anatoliegolovco/s4/reference/schematics/sintez2-keyboard.jpg

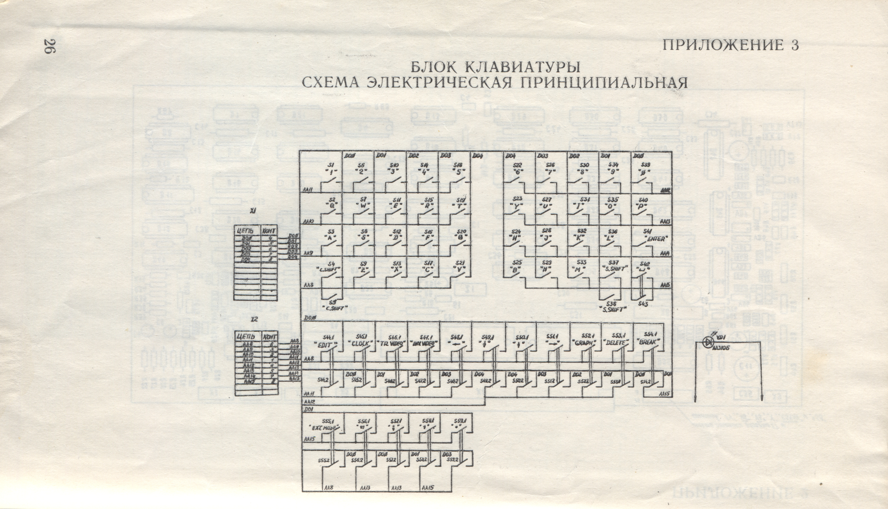
reference/schematics/sintez2-keyboard.jpg
