anatoliegolovco/s4/docs/ledger/architecture/README.md

# Topic: architecture

- **Created:** 2026-06-13
- **Status:** active

## Scope

Hardware/behavioral architecture decisions for the recreation and its model:
memory, DRAM timing, video arbitration, clock domains, and faithful-vs-improved
build targets.

## Questions

| Question file | Title | Status | Opened | Resolved |
| --- | --- | --- | --- | --- |
| [`dram-faithful-vs-improved.md`](./dram-faithful-vs-improved.md) | Faithful К565РУ5 timing vs modern SRAM in hardware? | open | 2026-06-13 | — |
| [`bank-switching-ram-size.md`](./bank-switching-ram-size.md) | How much RAM / what bank-switching scheme? | open | 2026-06-13 | — |
| [`schematic-bom-wiring-extraction.md`](./schematic-bom-wiring-extraction.md) | Mainboard BOM and wiring from the schematic | open | 2026-06-13 | — |
