anatoliegolovco/s4/docs/ledger/tooling/README.md

# Topic: tooling

- **Created:** 2026-06-13
- **Status:** active

## Scope

The tool stack and the zero-click control plane: KiCad, SimulIDE, ngspice, the
KiCad↔SimulIDE bridge, and how the LLM automates them through text.

## Questions

| Question file | Title | Status | Opened | Resolved |
| --- | --- | --- | --- | --- |
| [`schematic-automation-strategy.md`](./schematic-automation-strategy.md) | How does the LLM automate KiCad schematics in 2026? | resolved | 2026-06-13 | 2026-06-13 |
| [`cpu-soft-core-choice.md`](./cpu-soft-core-choice.md) | TV80 or A-Z80 for the simulation core? | open | 2026-06-13 | — |
