anatoliegolovco/s4/reference/board/sintez2-element-placement.jpg

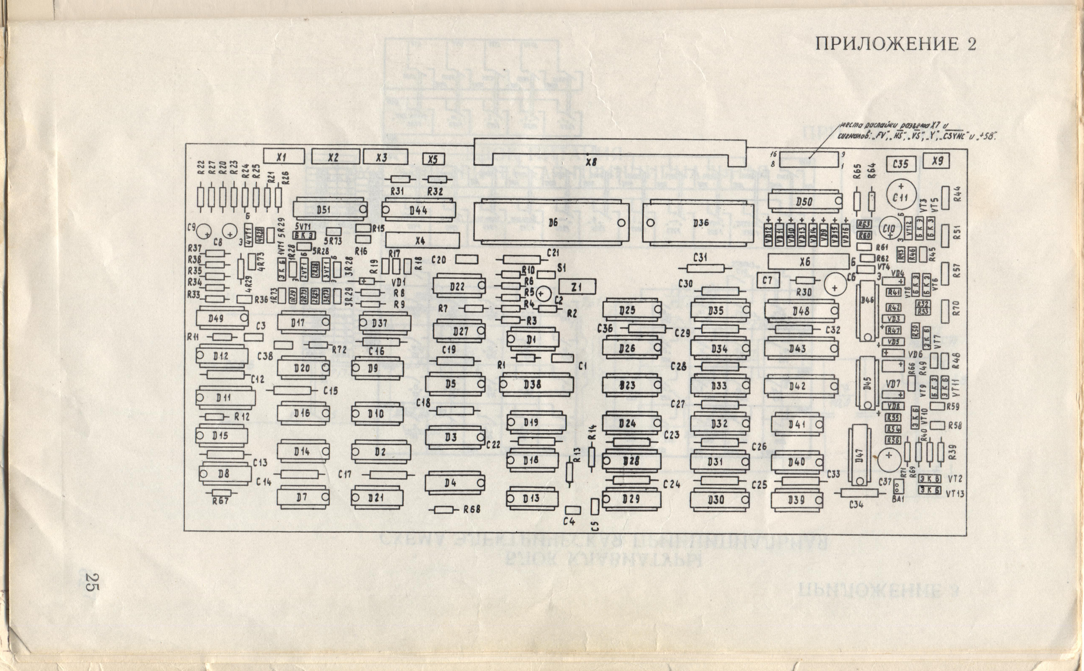
reference/board/sintez2-element-placement.jpg
