anatoliegolovco/s4/reference/photos/betadisk-original.png

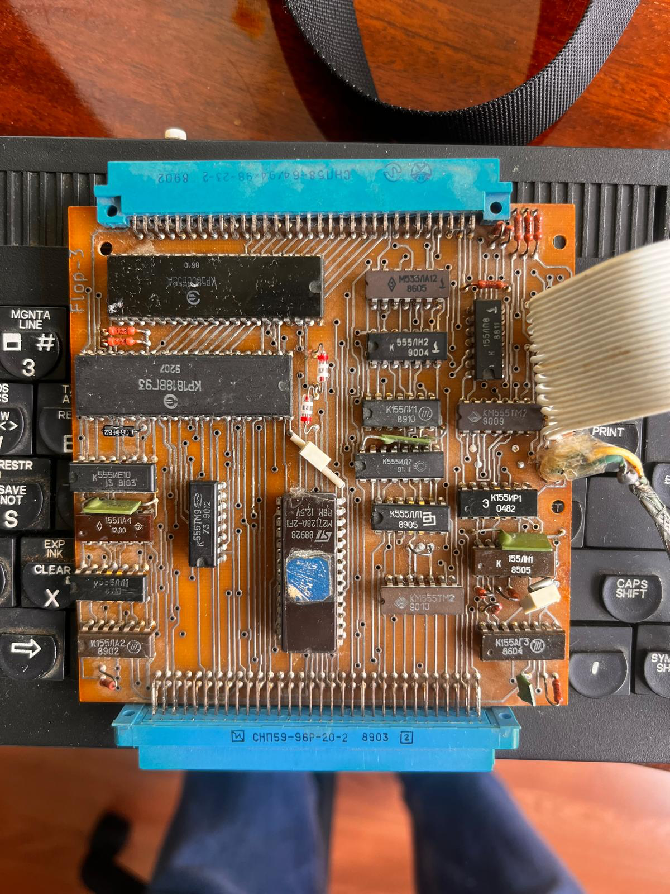
reference/photos/betadisk-original.png
