anatoliegolovco/s4/reference/photos/sintez2-board-habr.jpg

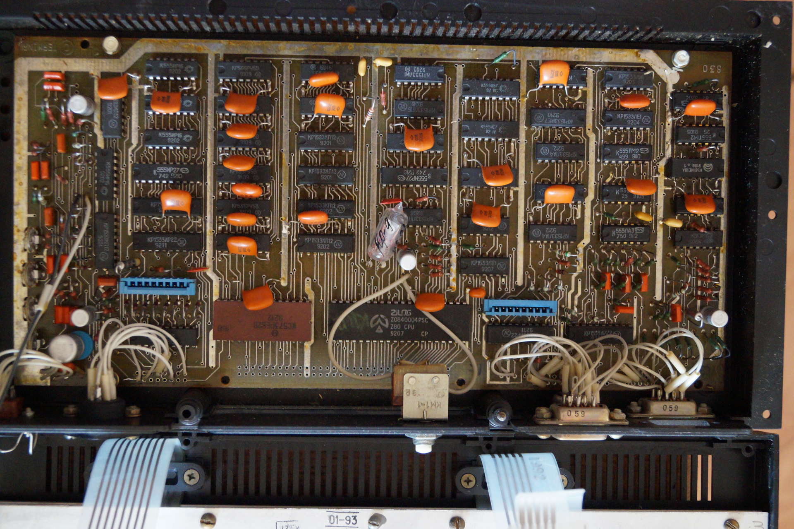
reference/photos/sintez2-board-habr.jpg
