anatoliegolovco/s4/reference/photos/sintez2-board-priborazbor.jpg

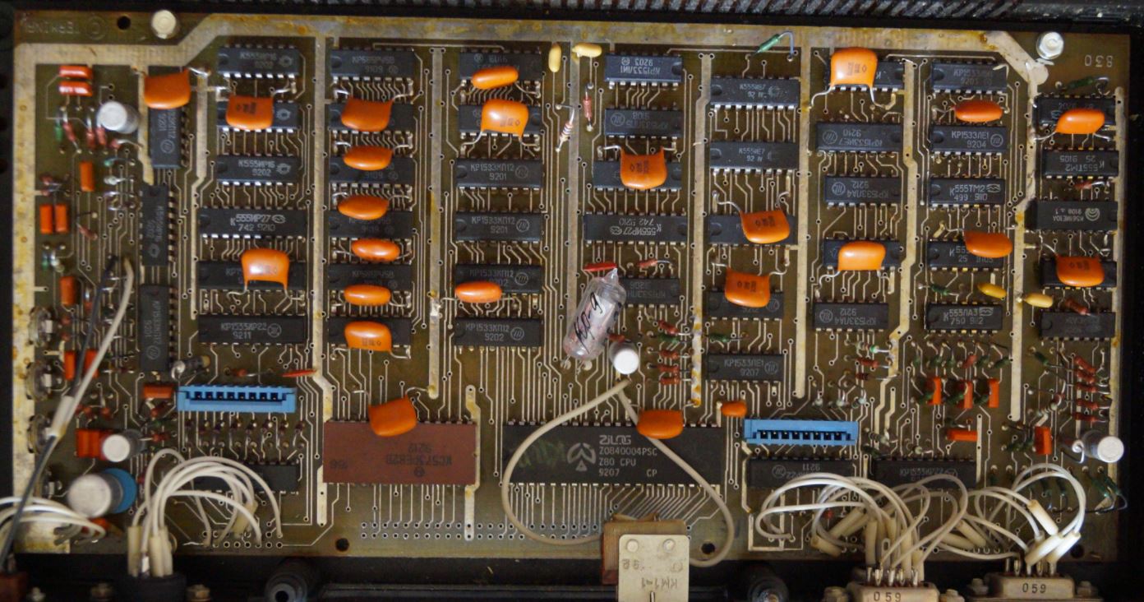
reference/photos/sintez2-board-priborazbor.jpg
