anatoliegolovco/s4/reference/photos/sintez2-rear-panel.jpg

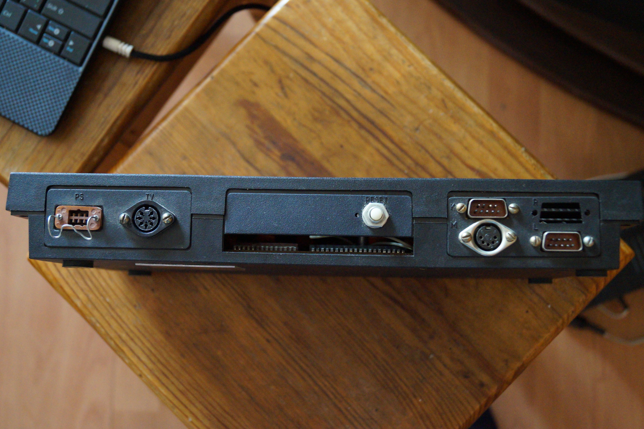
reference/photos/sintez2-rear-panel.jpg
