anatoliegolovco/s4/reference/photos/sintez128.jpg

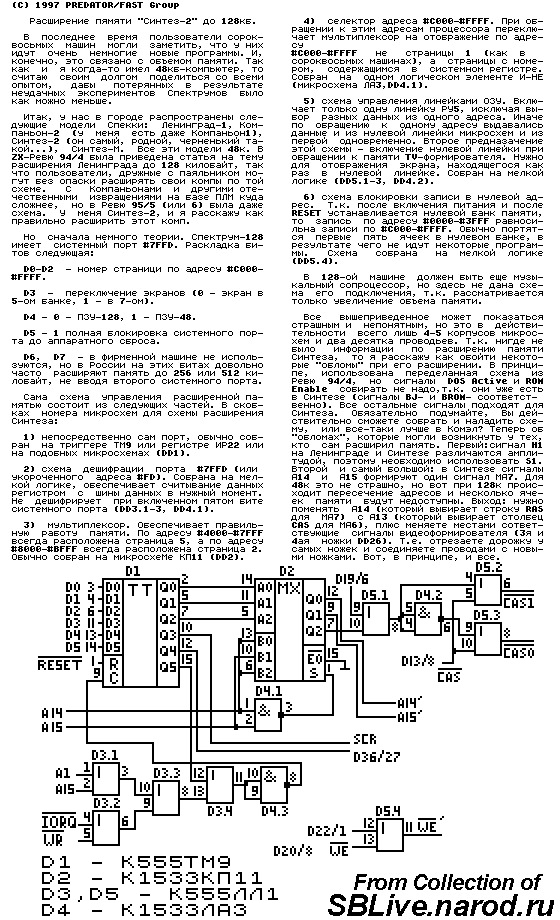
reference/photos/sintez128.jpg
