anatoliegolovco/s4/reference/pinouts/video-pinout.png

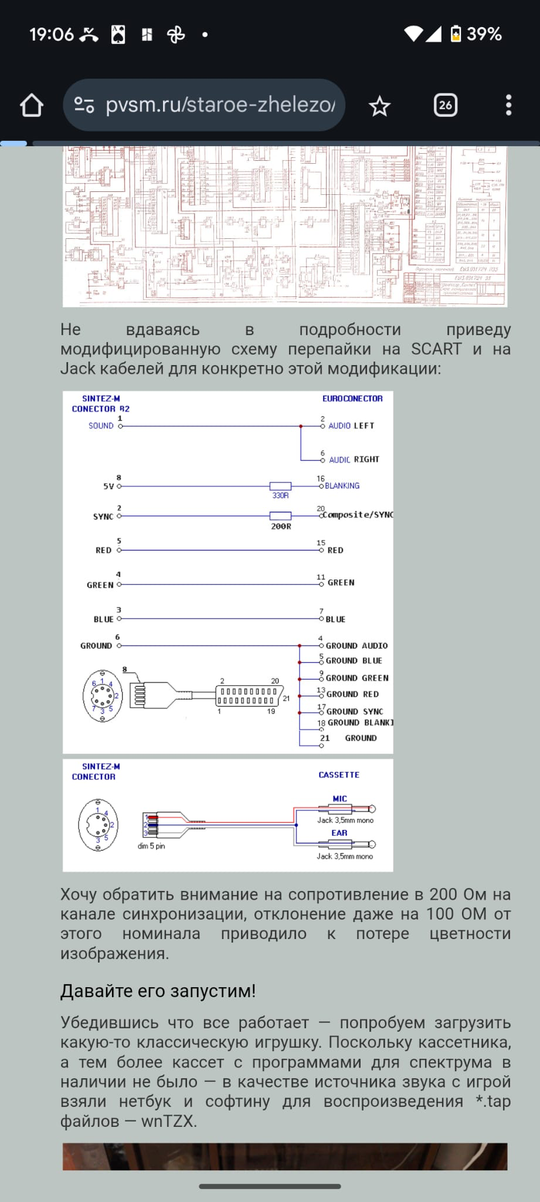
reference/pinouts/video-pinout.png
