anatoliegolovco/s4/reference/schematics/sintez2-power-supply.jpg

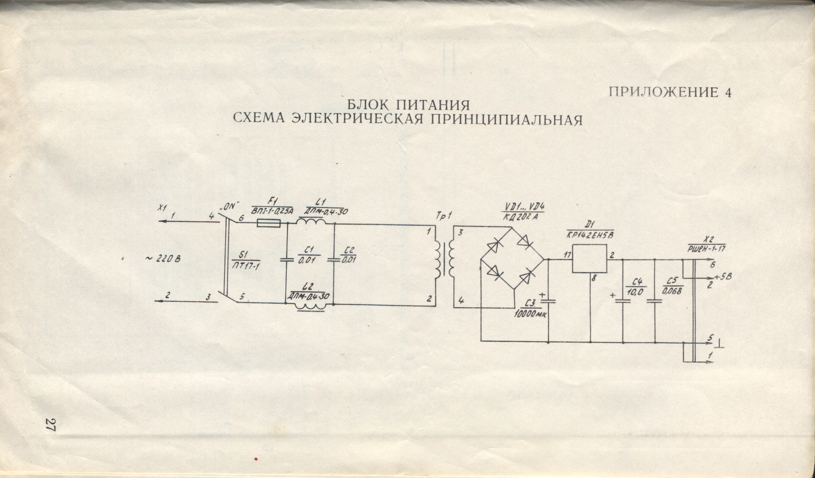
reference/schematics/sintez2-power-supply.jpg
