anatoliegolovco/s4/schematics/tiles-color/_grid_overview.png

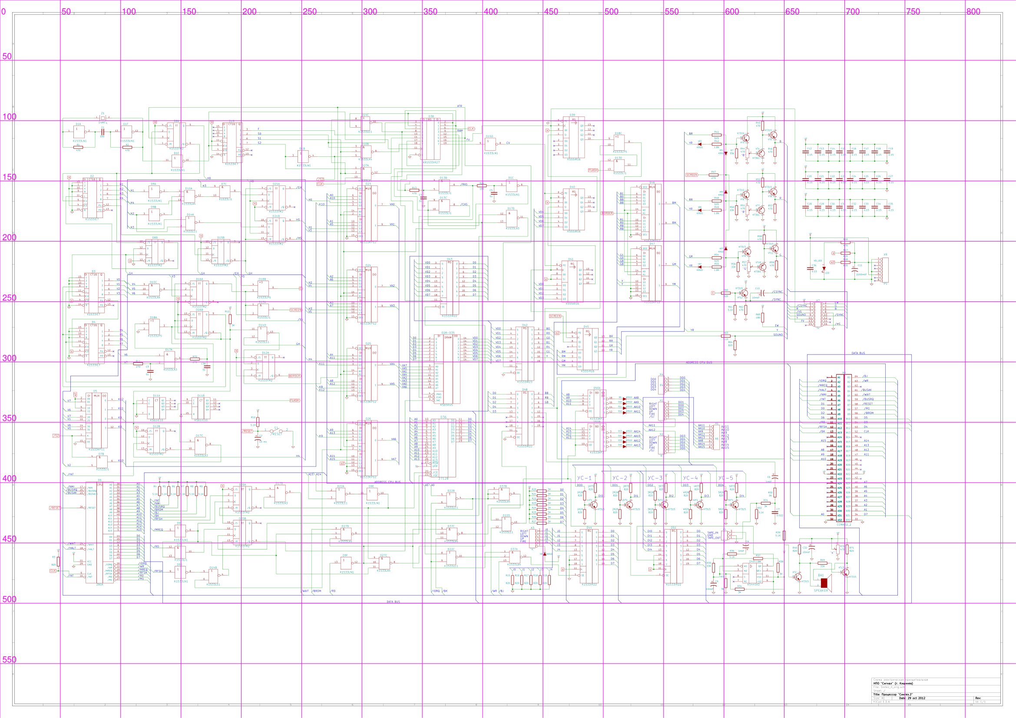
schematics/tiles-color/_grid_overview.png
