anatoliegolovco/s4/schematics/tiles-color/_overview.png

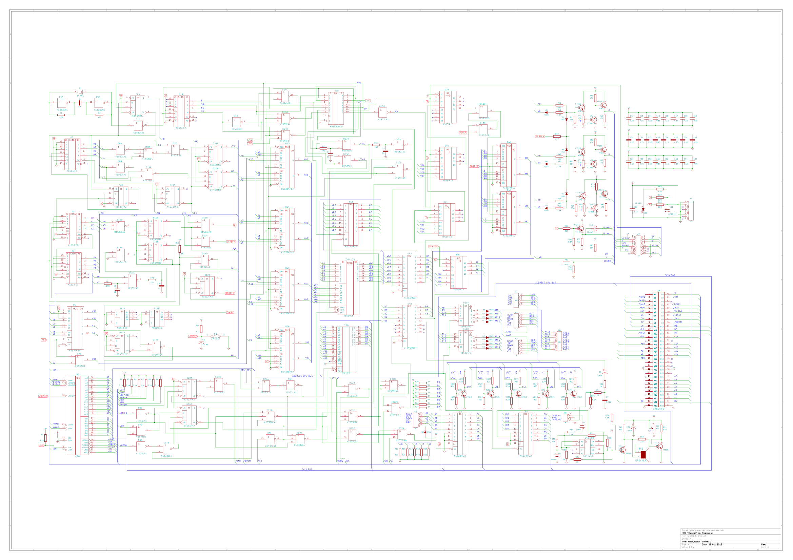
schematics/tiles-color/_overview.png
