anatoliegolovco/s4/schematics/tiles-color/c_r1c1.png

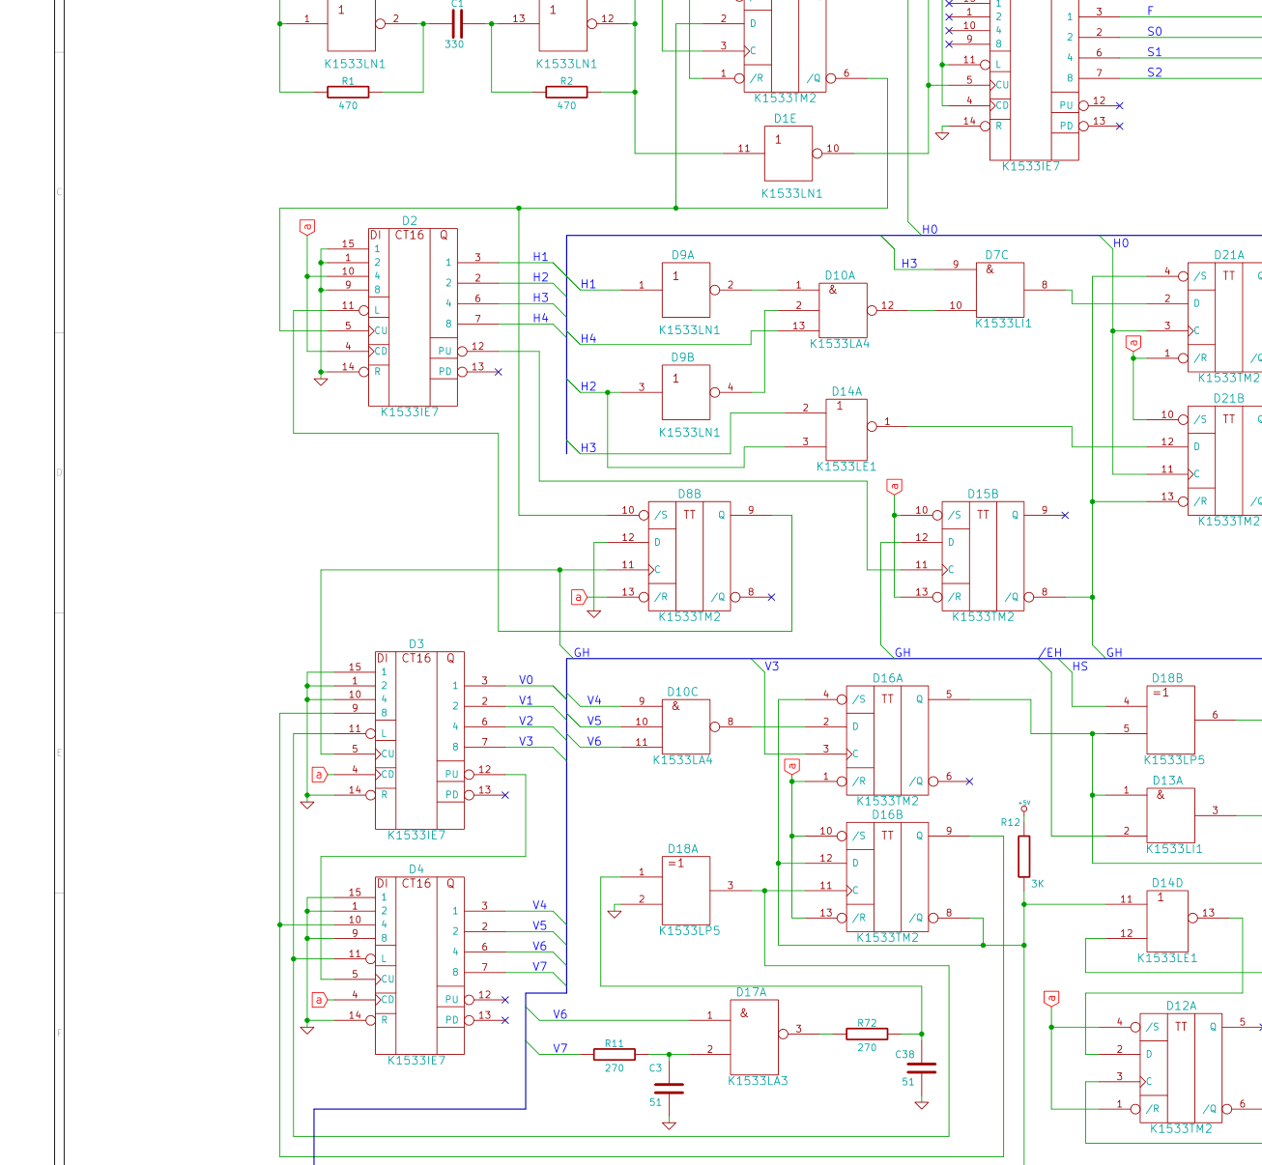
schematics/tiles-color/c_r1c1.png
