anatoliegolovco/s4/schematics/tiles-color/c_r1c2.png

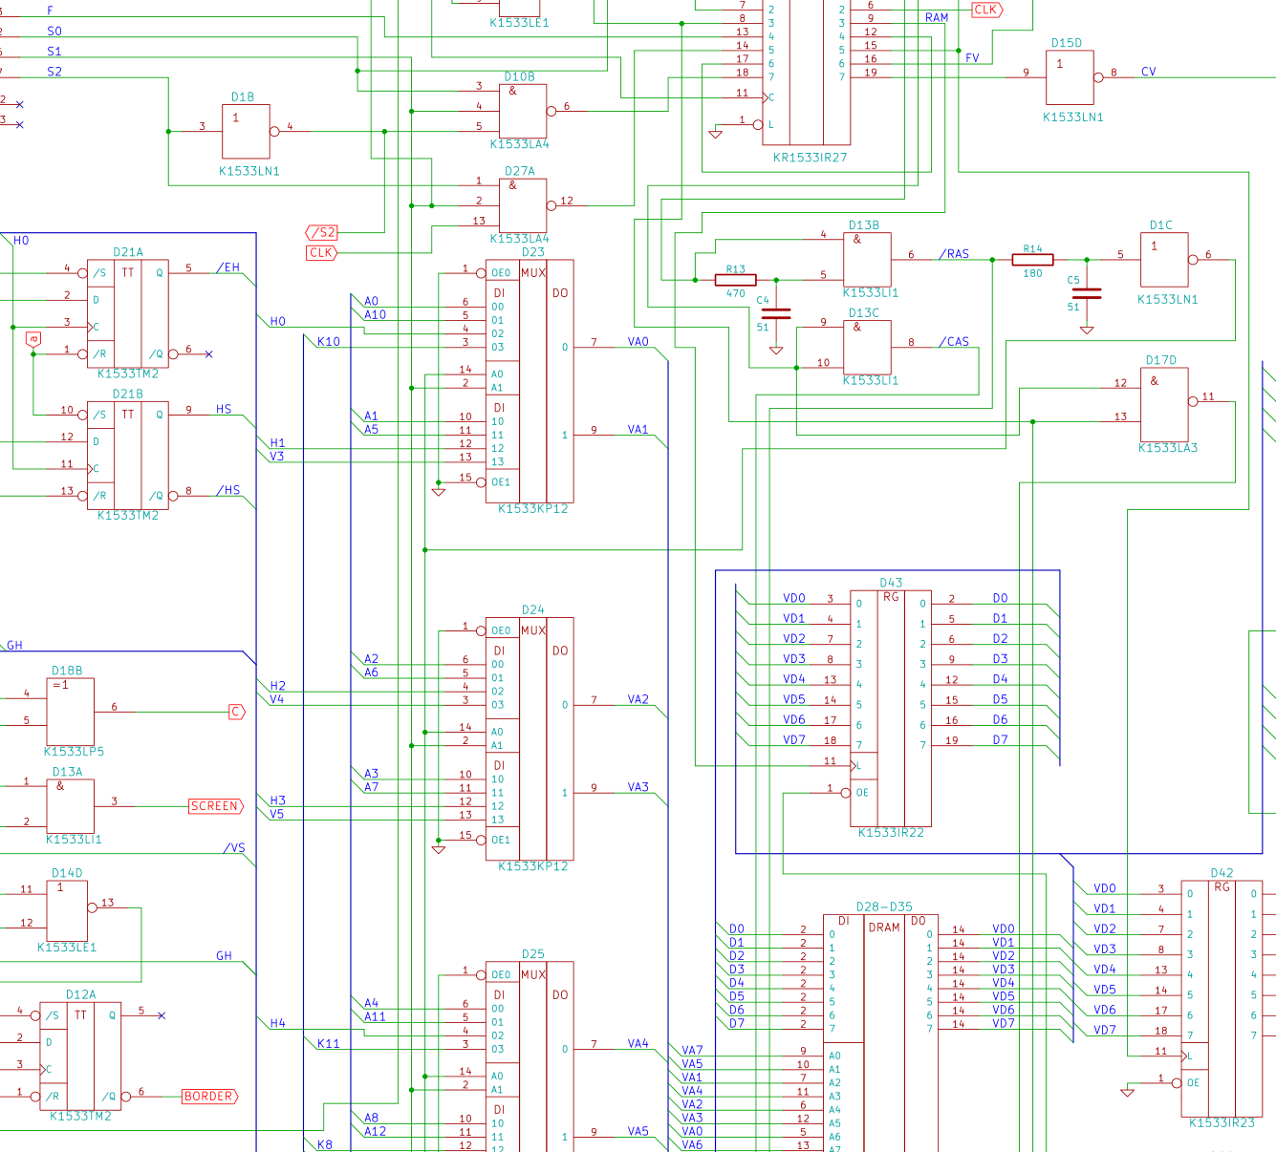
schematics/tiles-color/c_r1c2.png
