anatoliegolovco/s4/schematics/tiles-color/c_r1c3.png

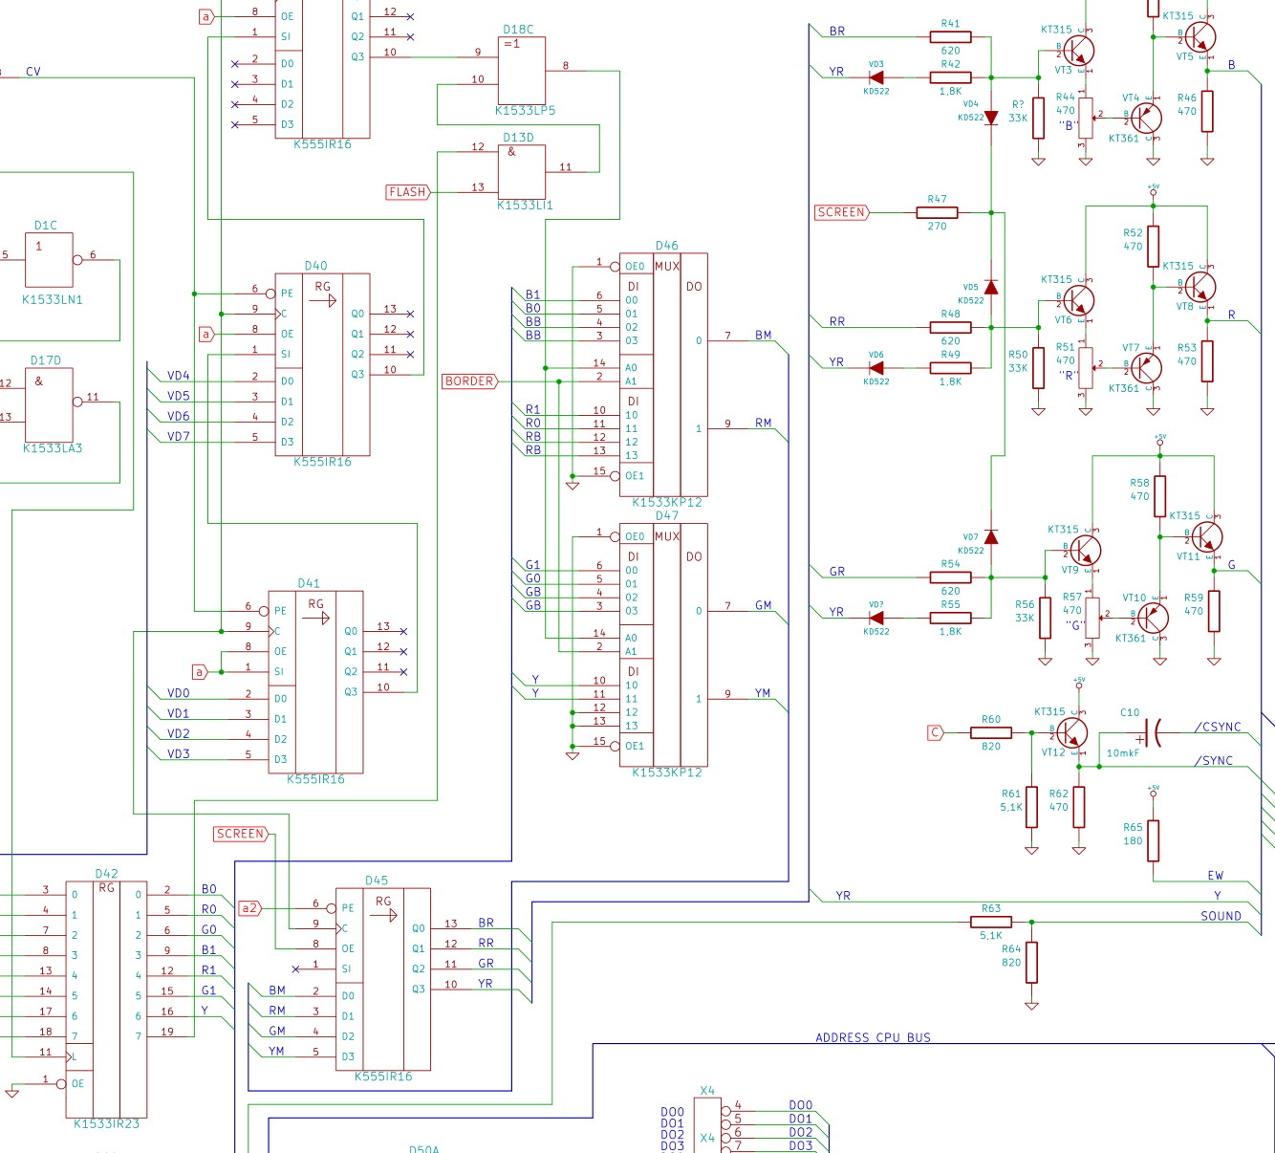
schematics/tiles-color/c_r1c3.png
