anatoliegolovco/s4/schematics/tiles-color/c_r1c4.png

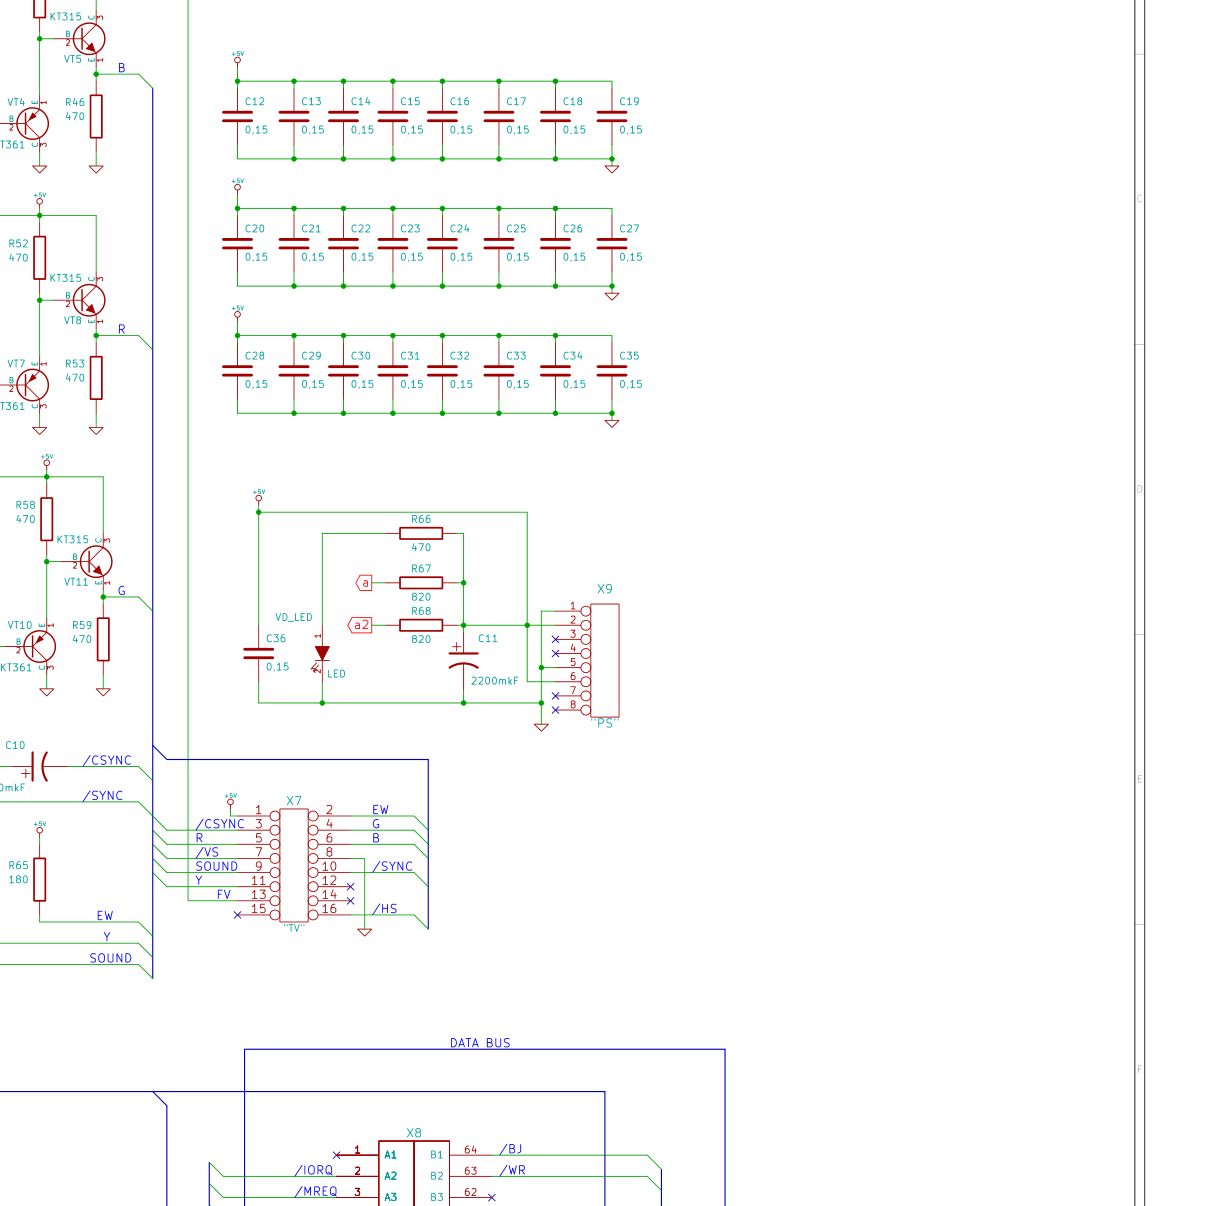
schematics/tiles-color/c_r1c4.png
