anatoliegolovco/s4/schematics/tiles-color/c_r2c1.png

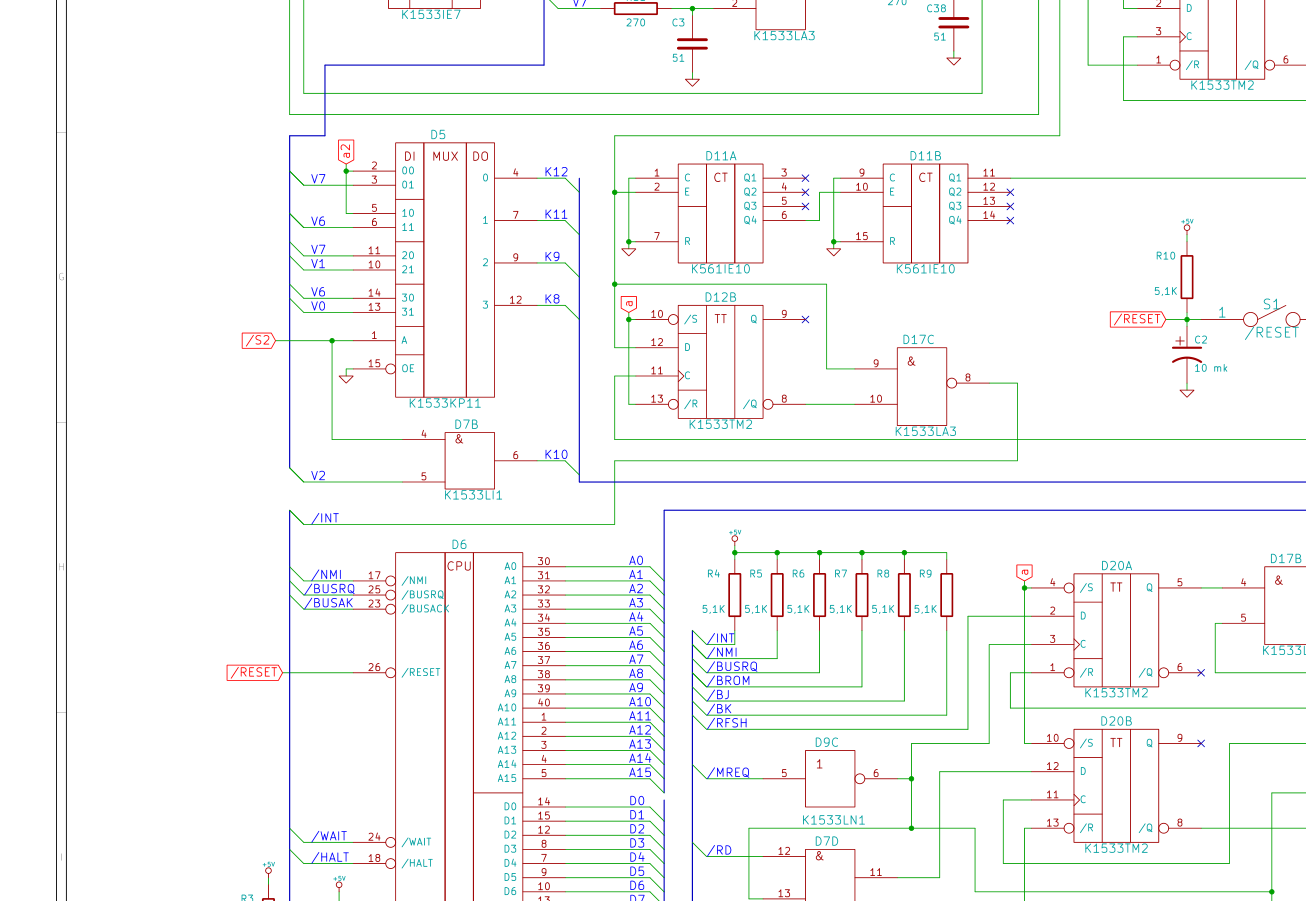
schematics/tiles-color/c_r2c1.png
