anatoliegolovco/s4/schematics/tiles-color/c_r2c2.png

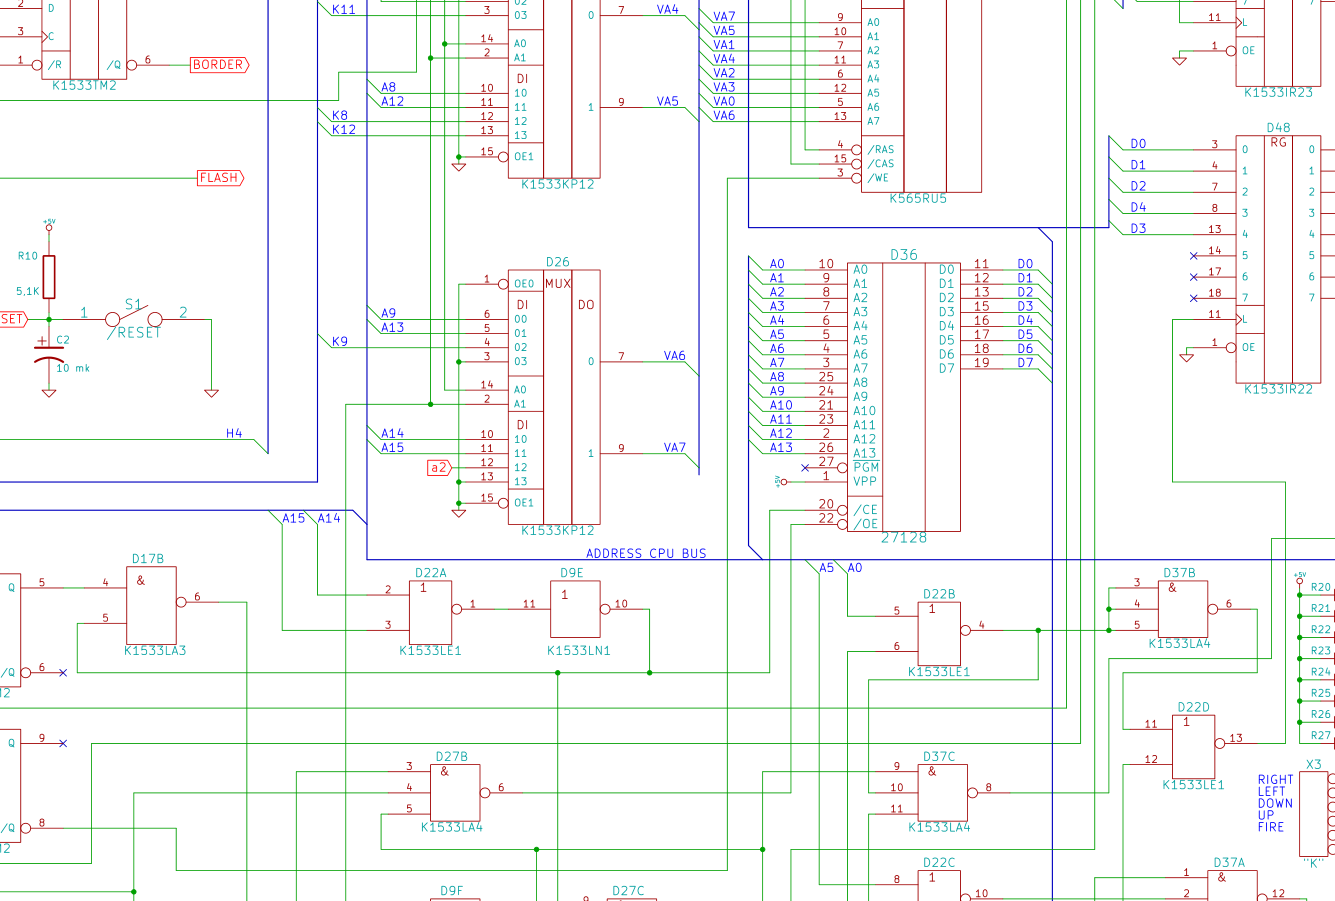
schematics/tiles-color/c_r2c2.png
