anatoliegolovco/s4/schematics/tiles-color/c_r2c3.png

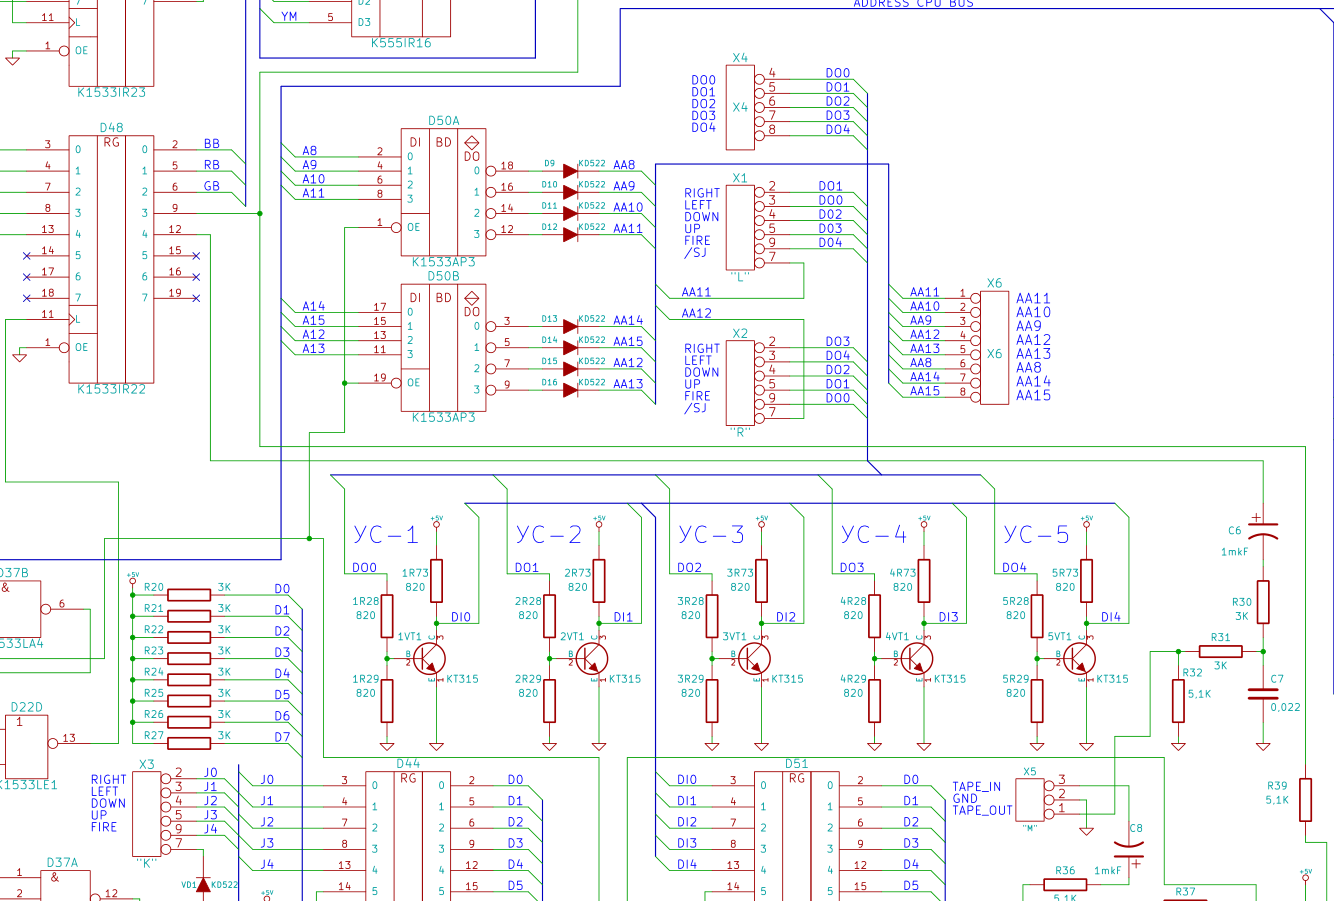
schematics/tiles-color/c_r2c3.png
