anatoliegolovco/s4/schematics/tiles-color/c_r2c4.png

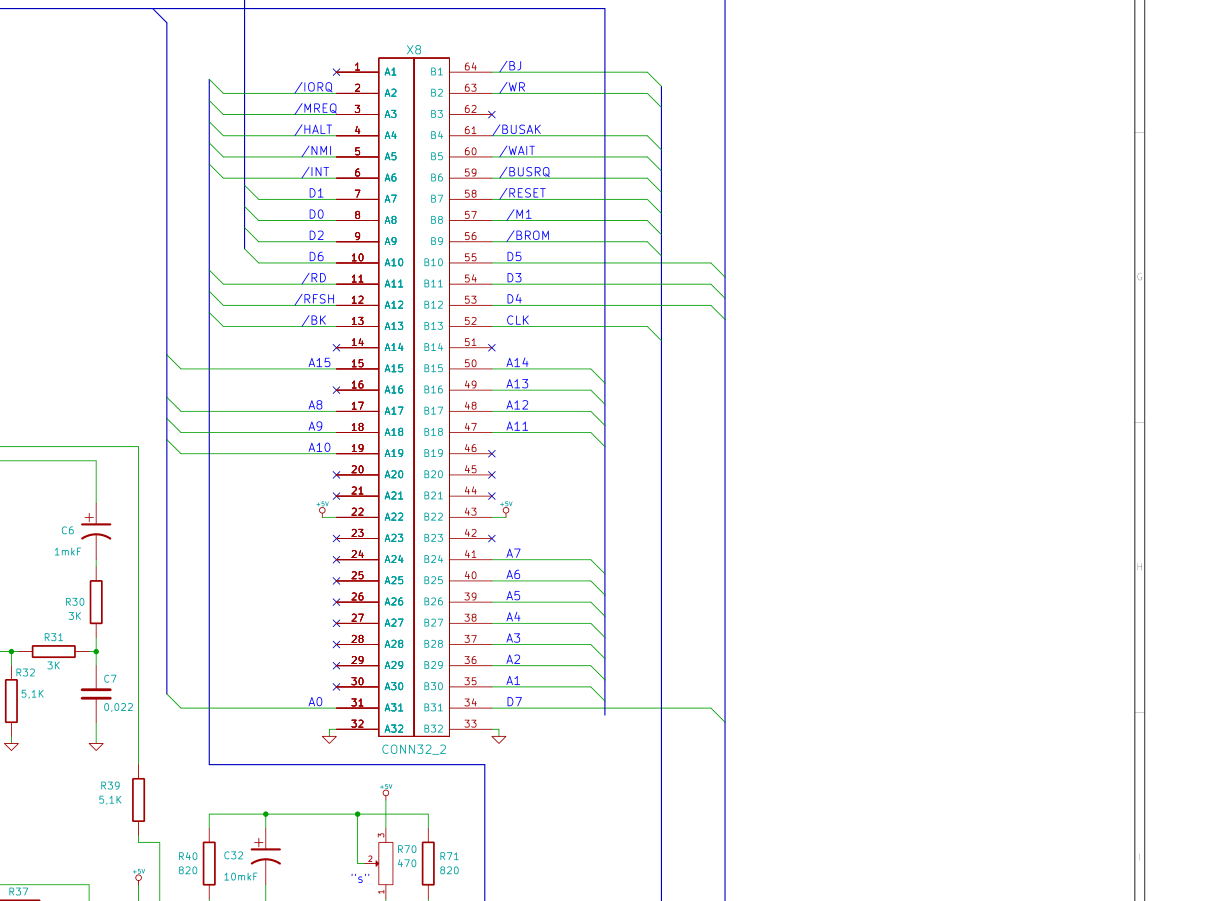
schematics/tiles-color/c_r2c4.png
