anatoliegolovco/s4/schematics/tiles-color/c_r3c1.png

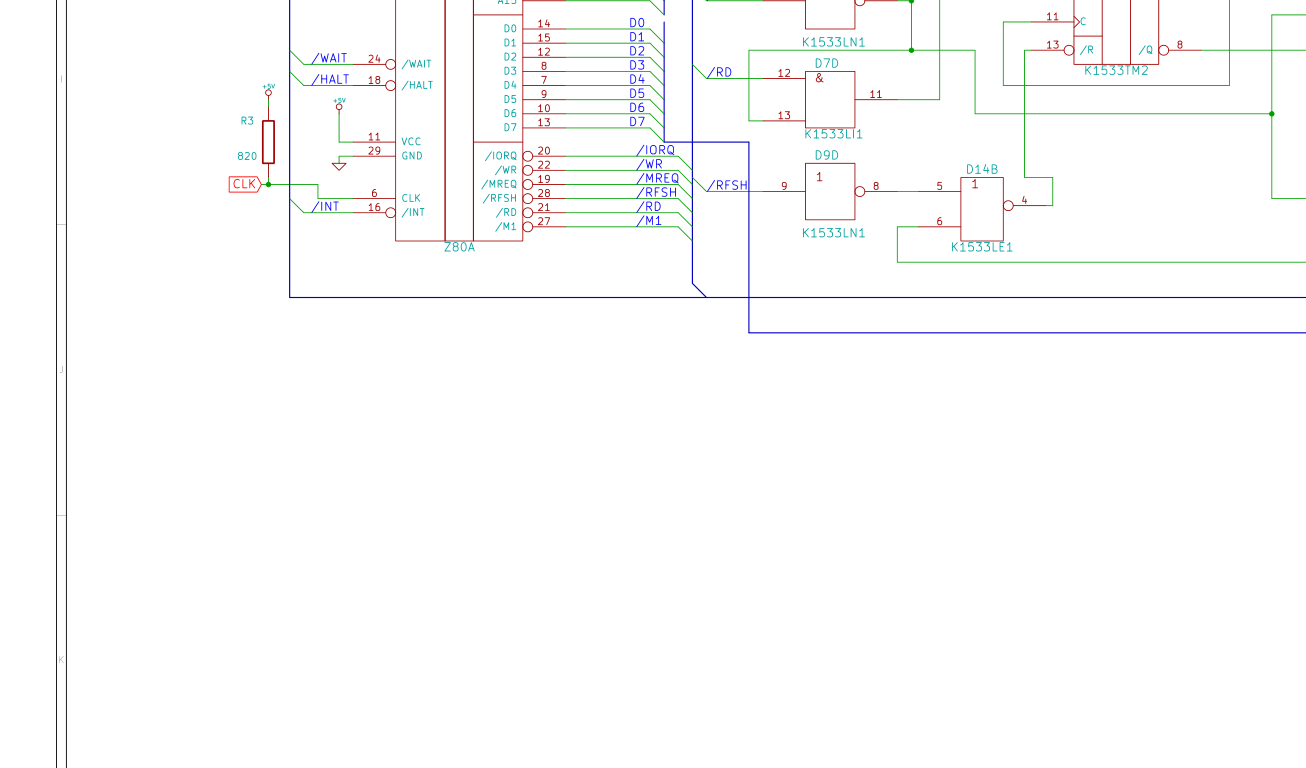
schematics/tiles-color/c_r3c1.png
