anatoliegolovco/s4/schematics/tiles-color/c_r3c2.png

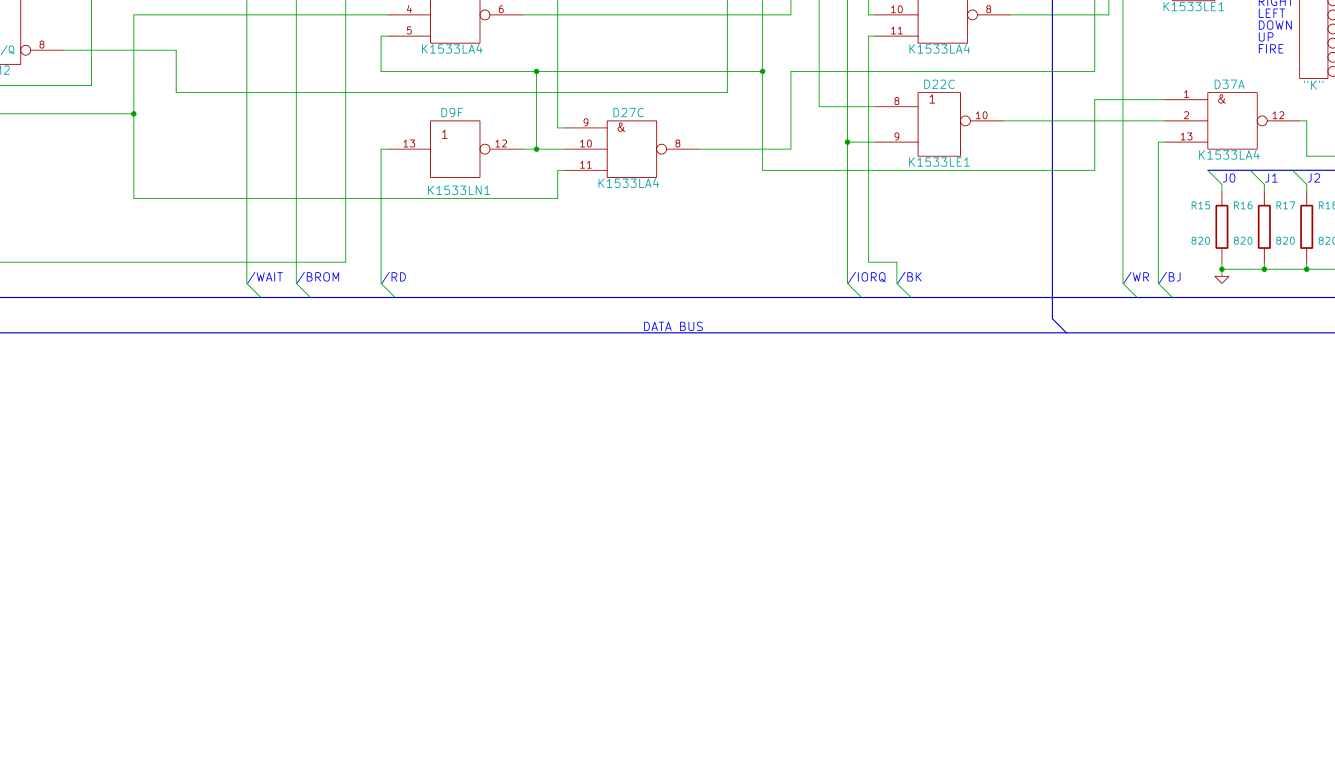
schematics/tiles-color/c_r3c2.png
