anatoliegolovco/s4/schematics/tiles-color/c_r3c3.png

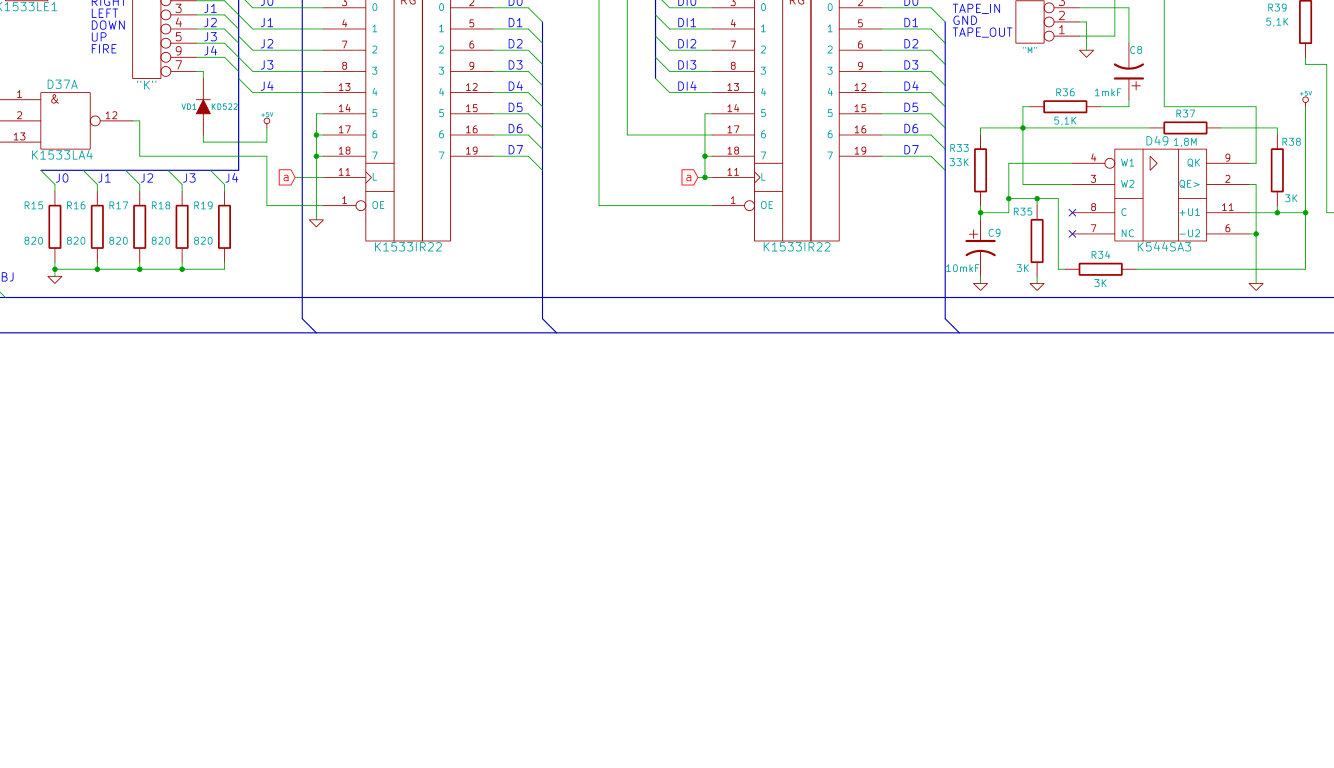
schematics/tiles-color/c_r3c3.png
