anatoliegolovco/s4/schematics/tiles-color/layers/layer_blue.png

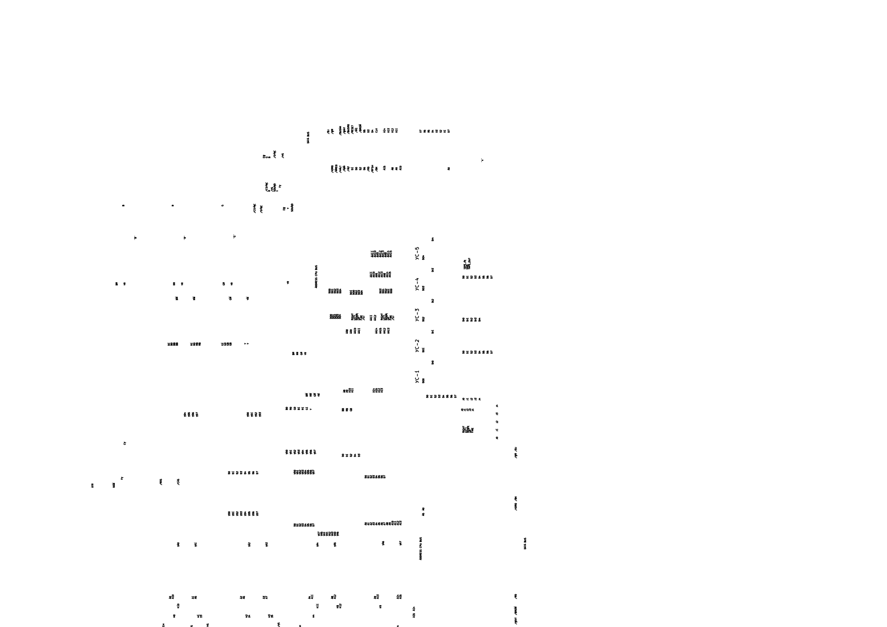
schematics/tiles-color/layers/layer_blue.png
