anatoliegolovco/s4/schematics/tiles-color/layers/layer_cyan.png

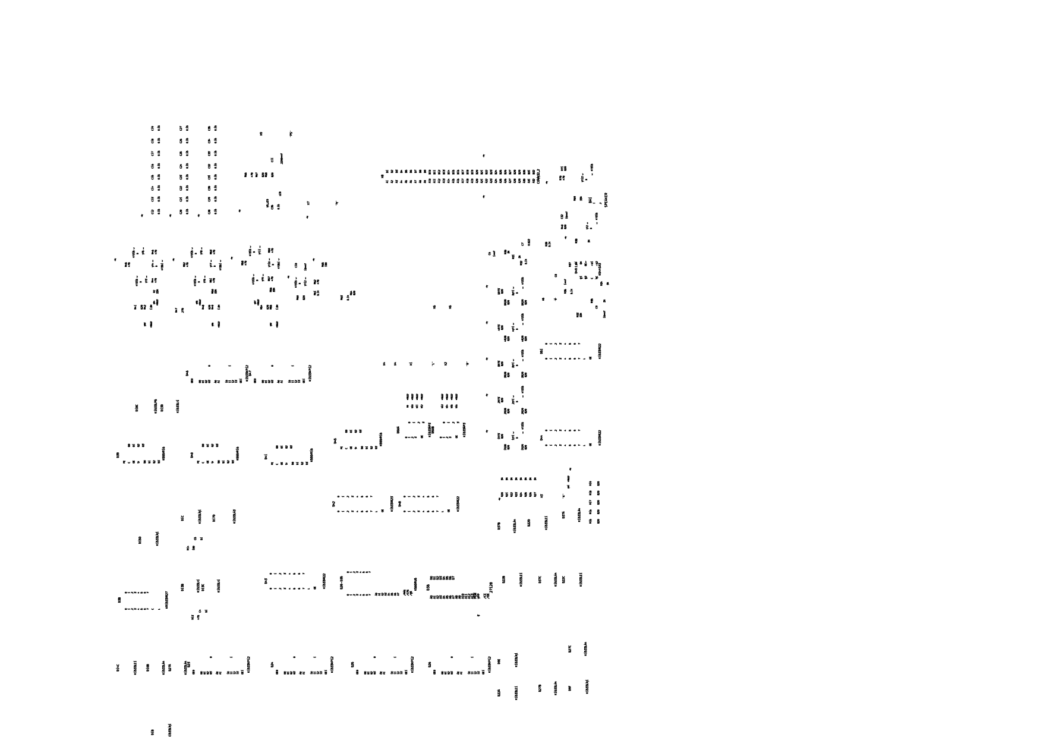
schematics/tiles-color/layers/layer_cyan.png
