anatoliegolovco/s4/schematics/tiles-color/layers/layer_darkred.png

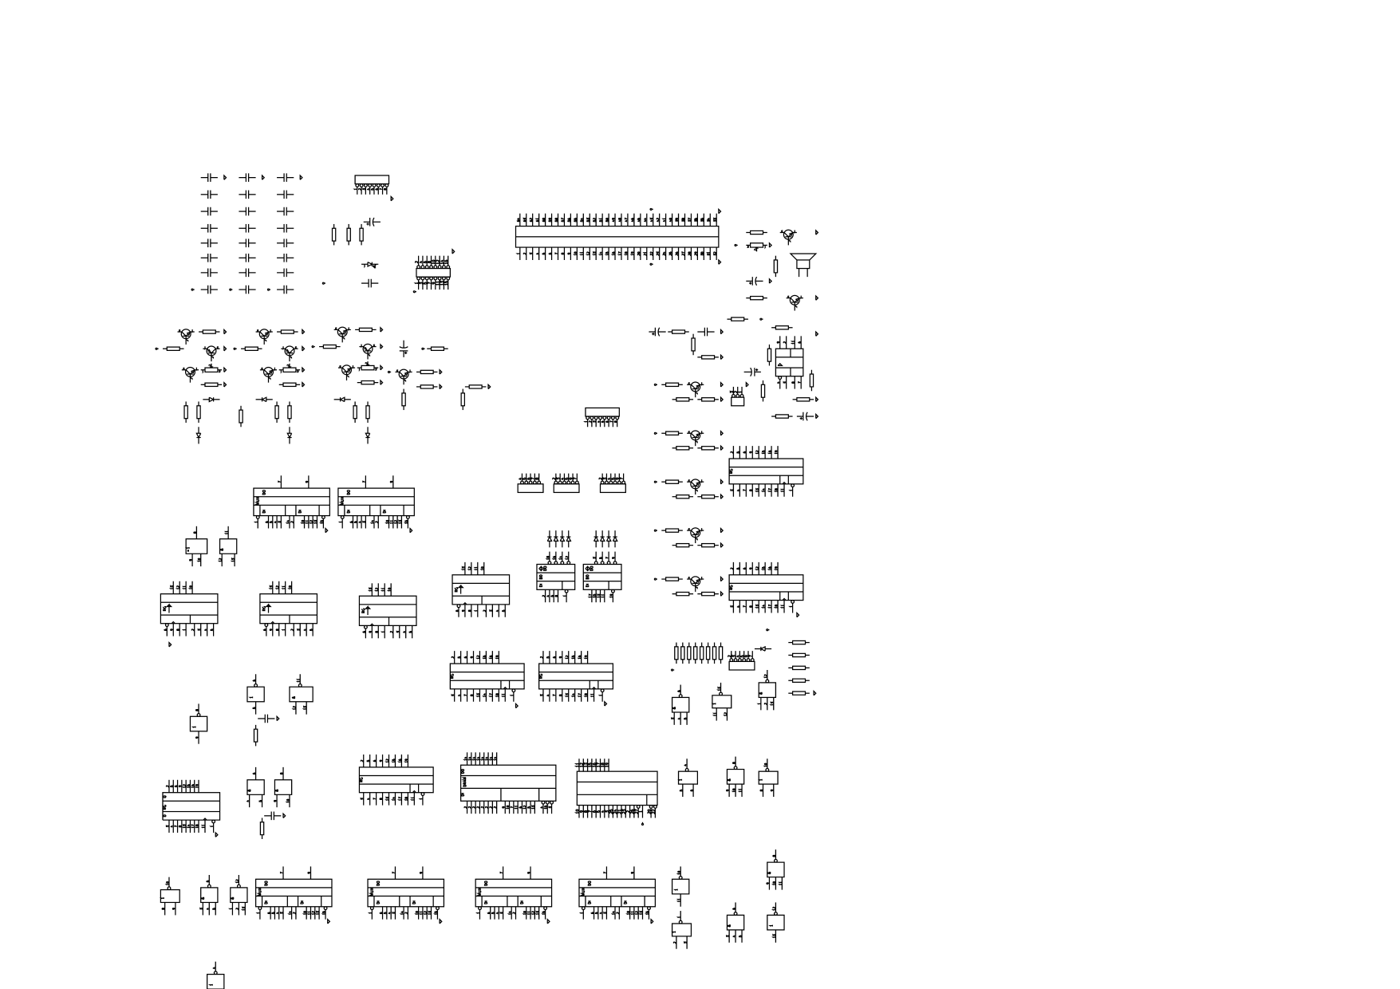
schematics/tiles-color/layers/layer_darkred.png
