anatoliegolovco/s4/schematics/tiles-color/layers/layer_dkblue.png

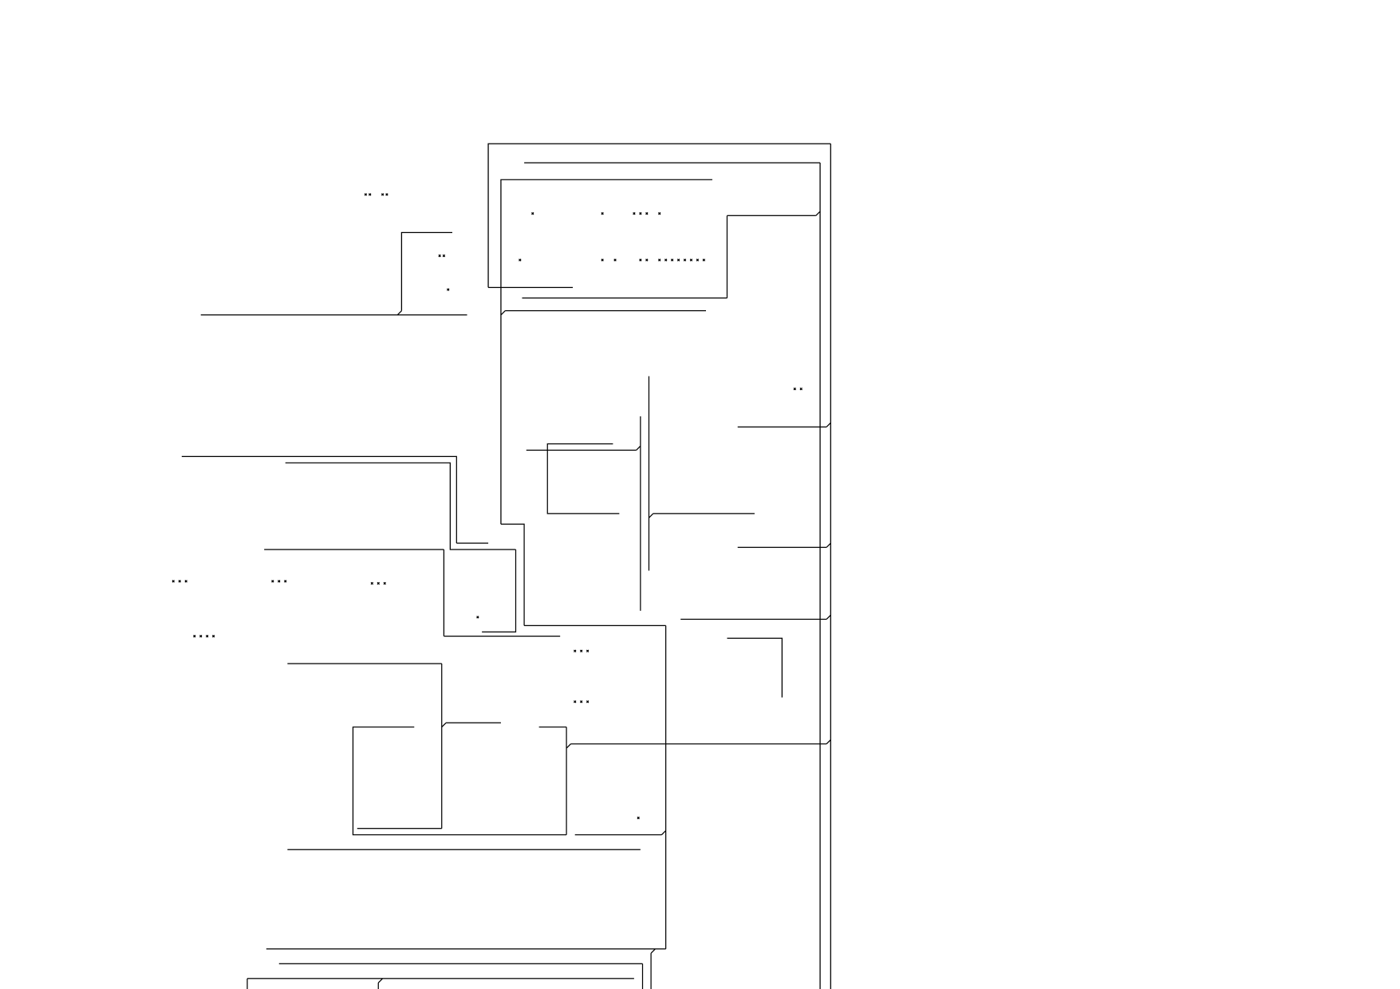
schematics/tiles-color/layers/layer_dkblue.png
