anatoliegolovco/s4/schematics/tiles-color/layers/layer_green.png

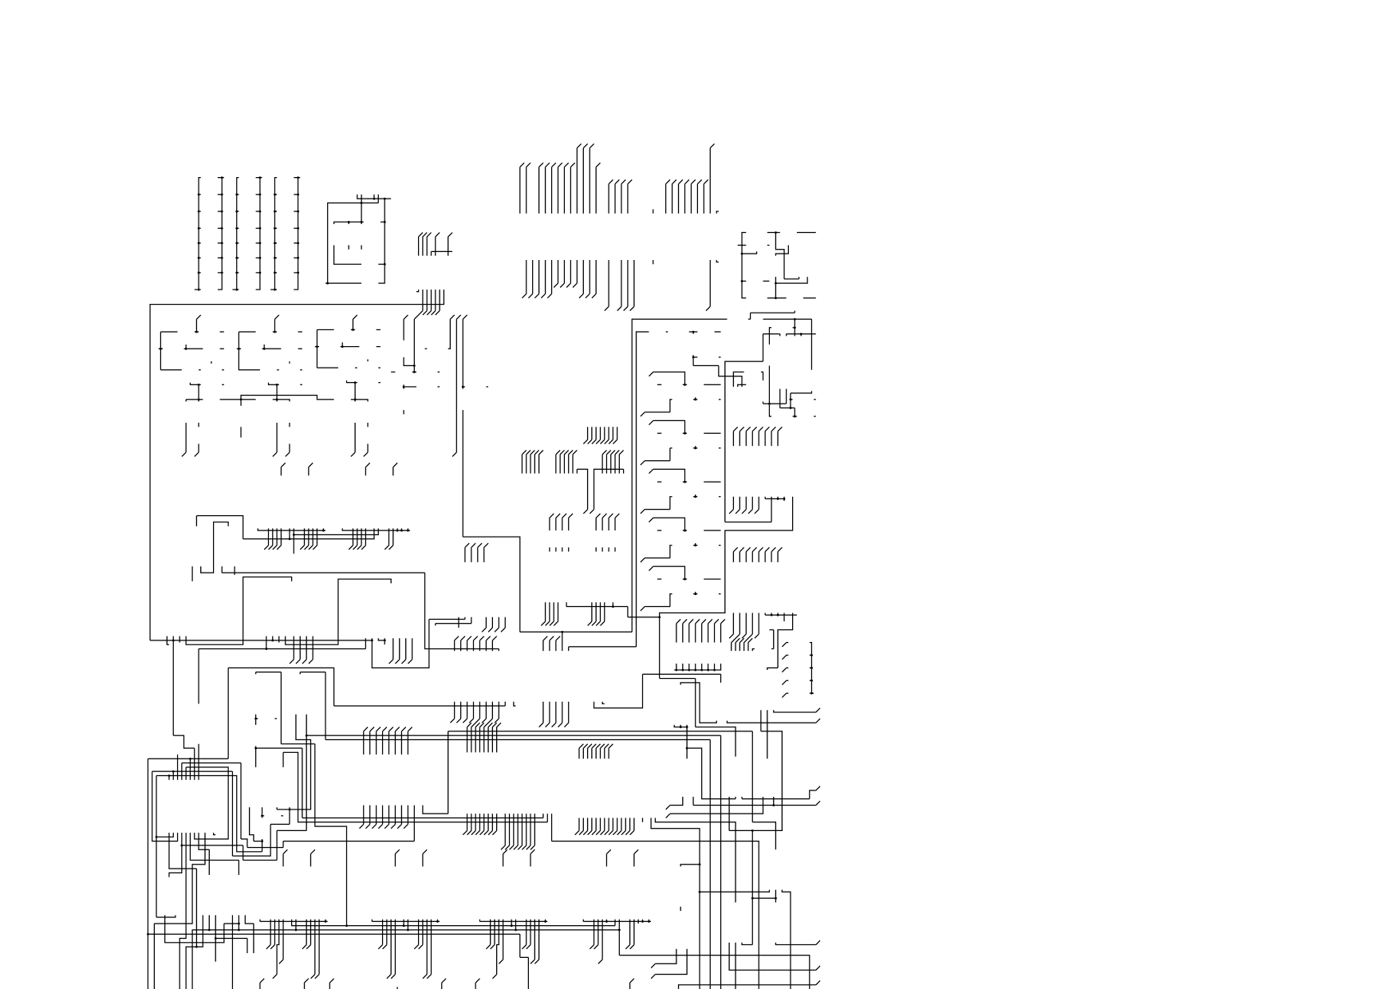
schematics/tiles-color/layers/layer_green.png
