anatoliegolovco/s4/schematics/tiles-color/zoom/gap_bot_center.png

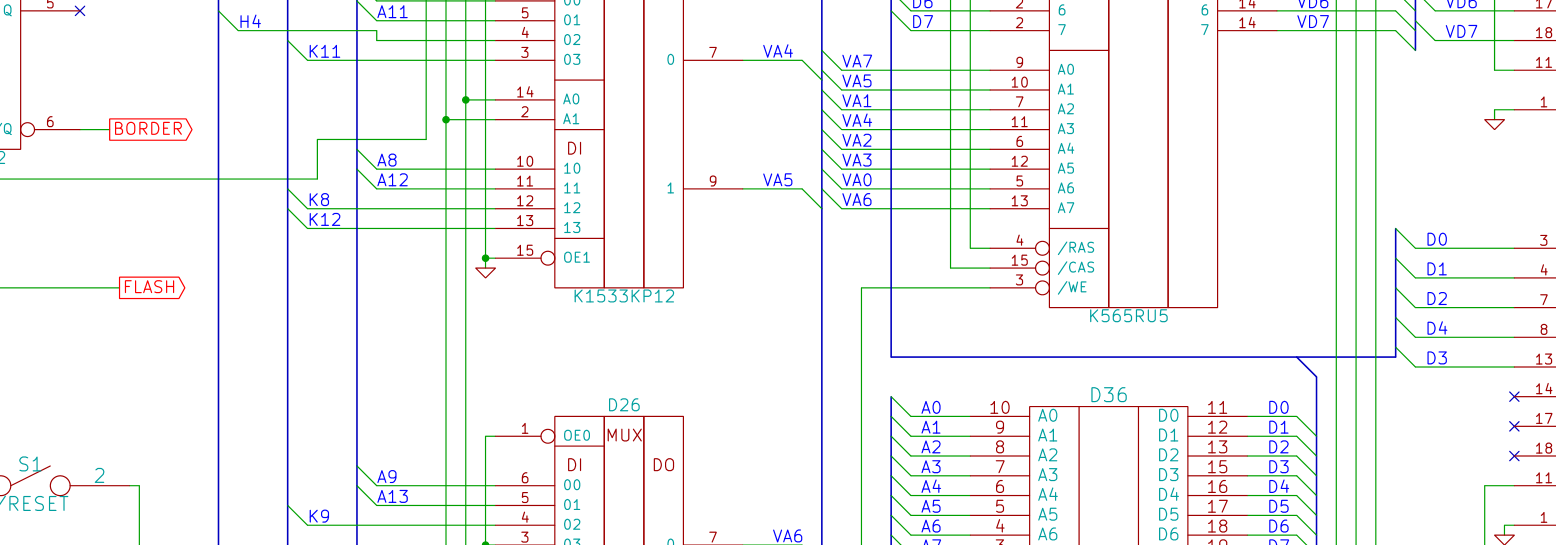
schematics/tiles-color/zoom/gap_bot_center.png
