anatoliegolovco/s4/schematics/tiles-color/zoom/gap_bot_left.png

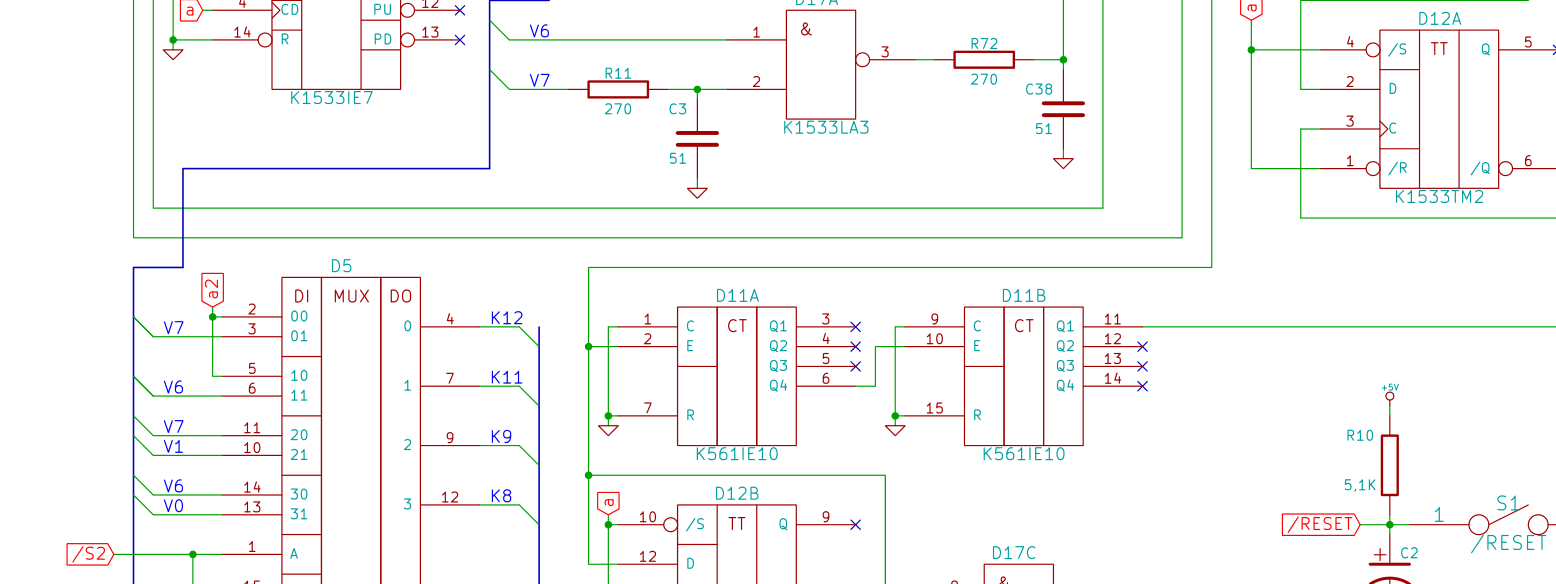
schematics/tiles-color/zoom/gap_bot_left.png
