anatoliegolovco/s4/schematics/tiles-color/zoom/gap_mid_right.png

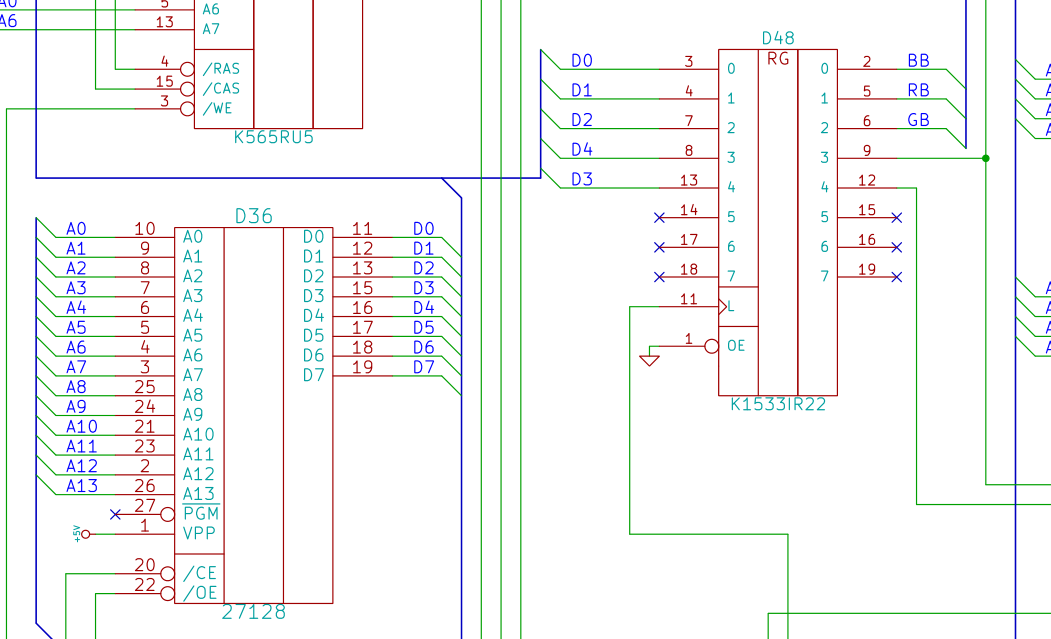
schematics/tiles-color/zoom/gap_mid_right.png
