anatoliegolovco/s4/schematics/tiles-color/zoom/zoom_connector.png

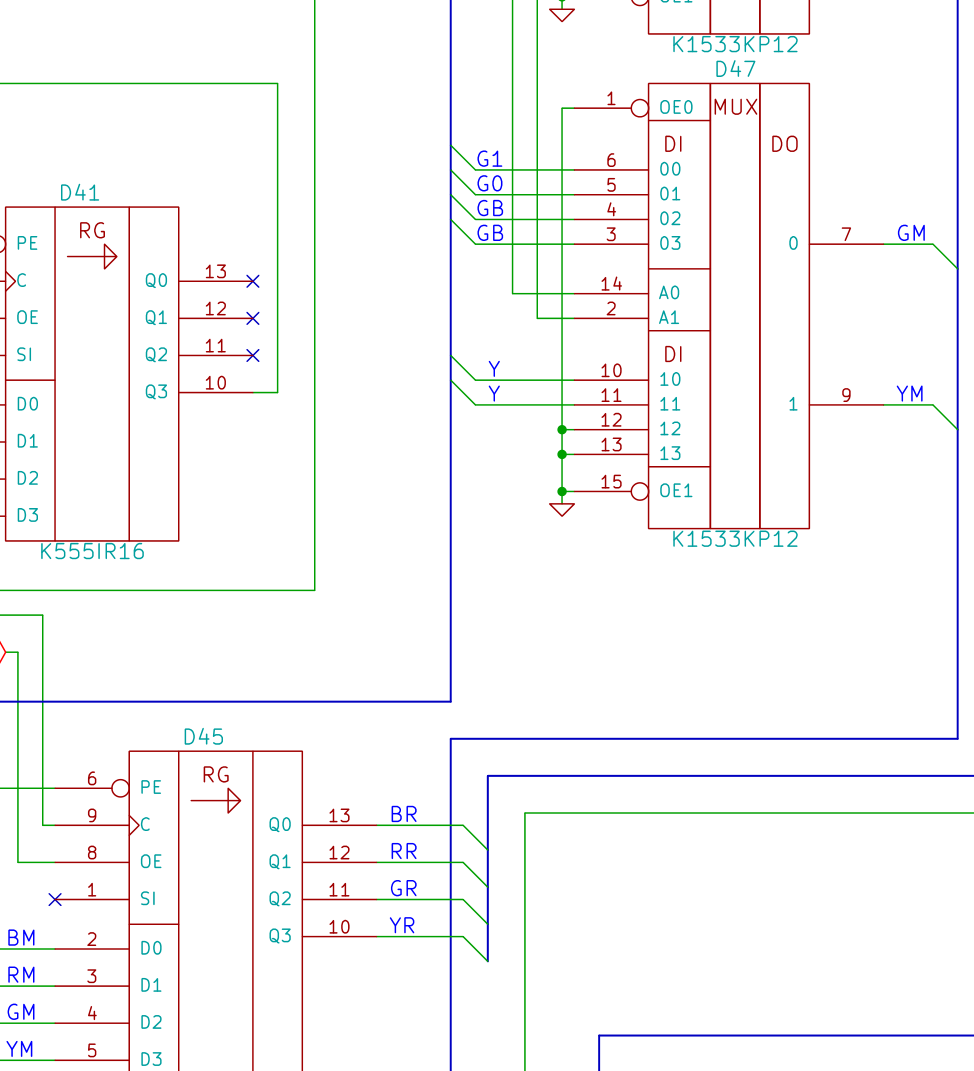
schematics/tiles-color/zoom/zoom_connector.png
