anatoliegolovco/s4/schematics/tiles-color/zoom/zoom_dram.png

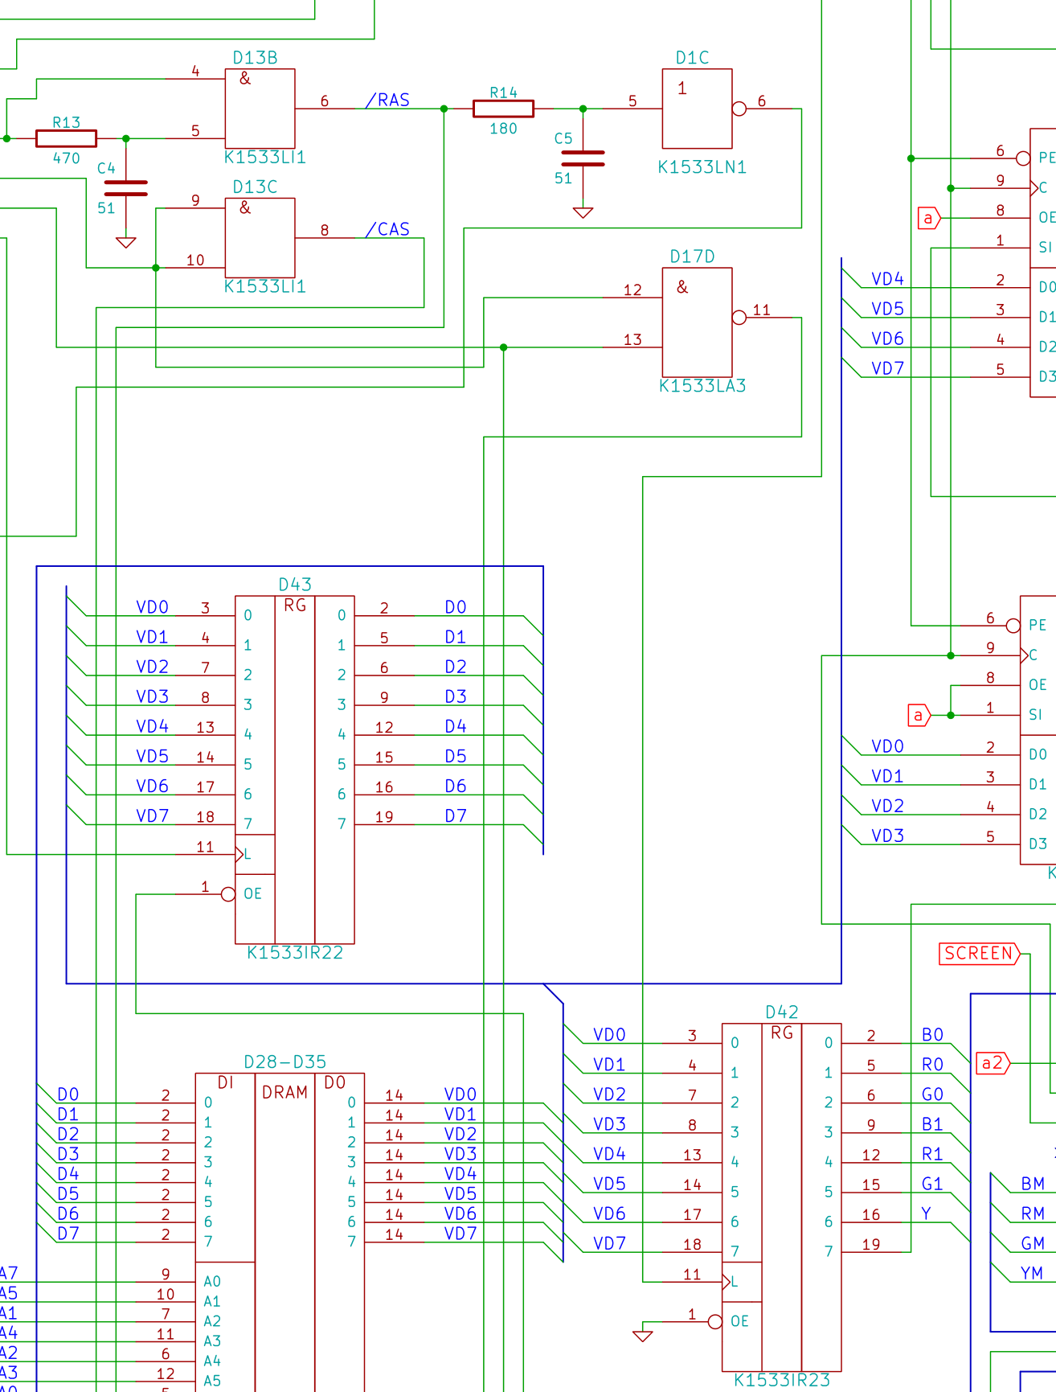
schematics/tiles-color/zoom/zoom_dram.png
