anatoliegolovco/s4/schematics/tiles-color/zoom/zoom_edge.png

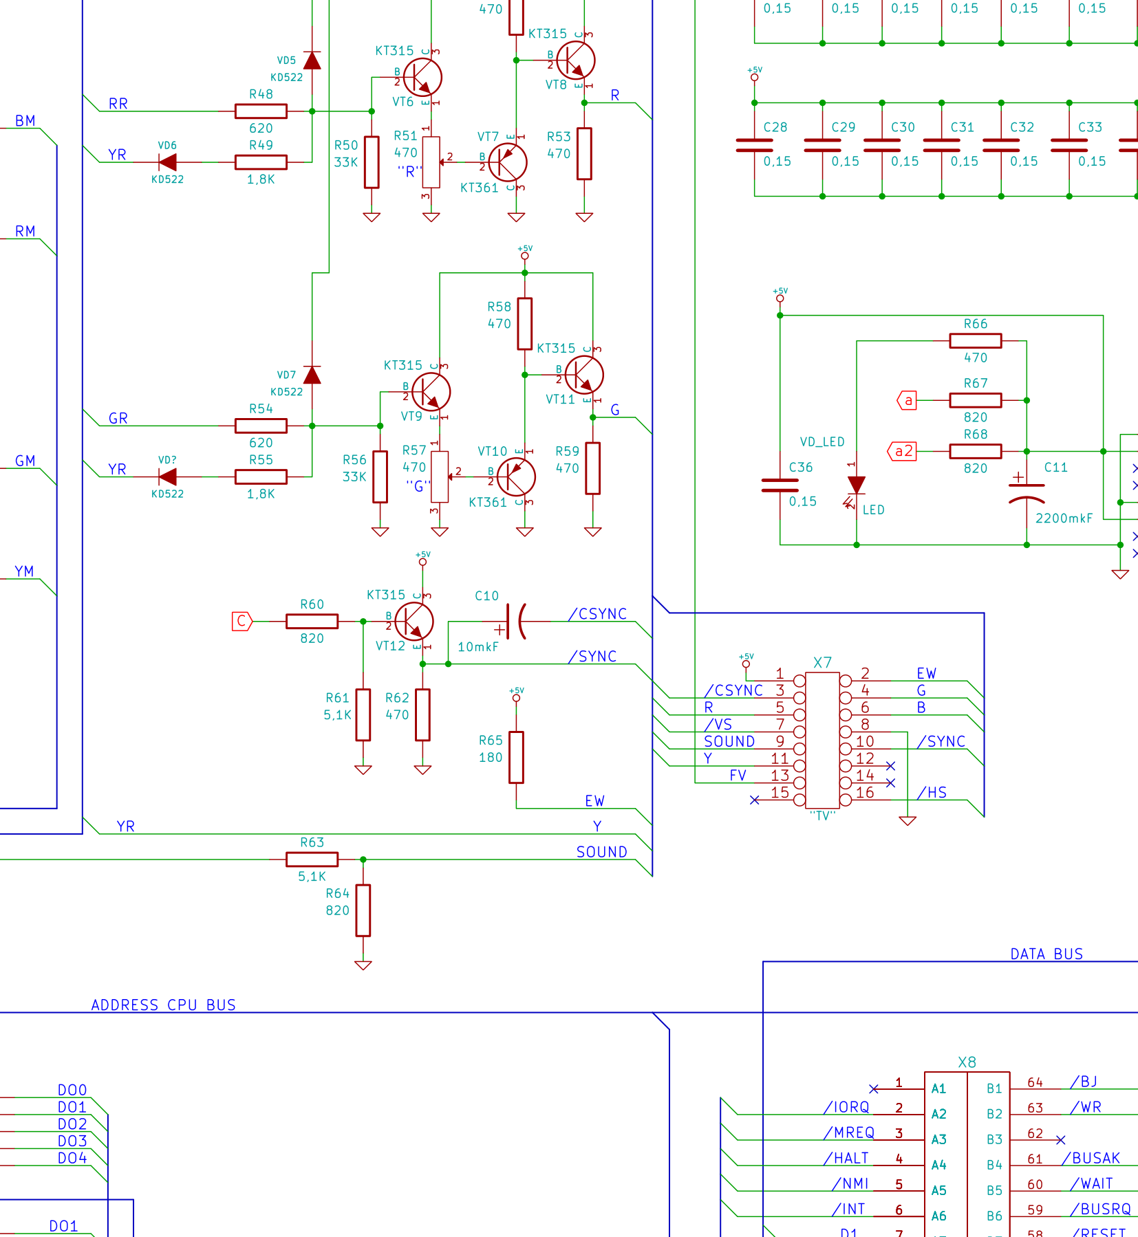
schematics/tiles-color/zoom/zoom_edge.png
