anatoliegolovco/s4/schematics/tiles-color/zoom/zoom_rom_lowleft.png

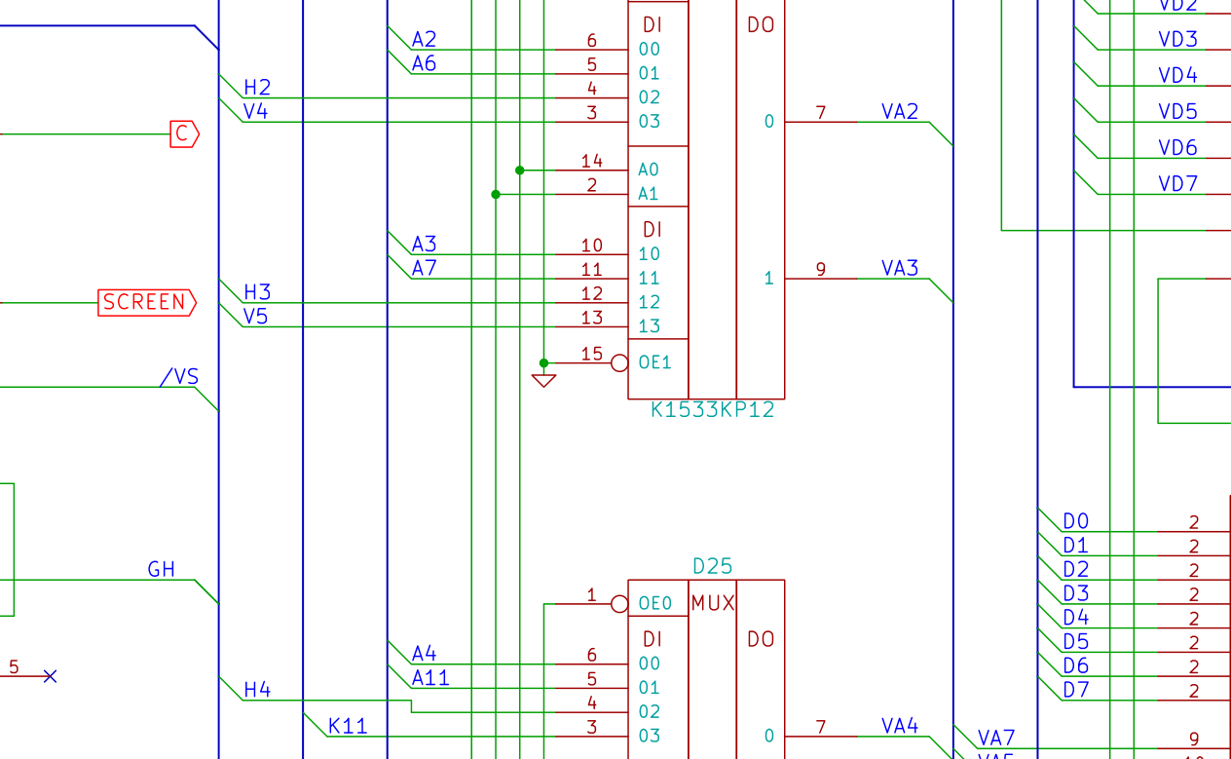
schematics/tiles-color/zoom/zoom_rom_lowleft.png
