anatoliegolovco/s4/schematics/tiles/_right_connectors_bot.png

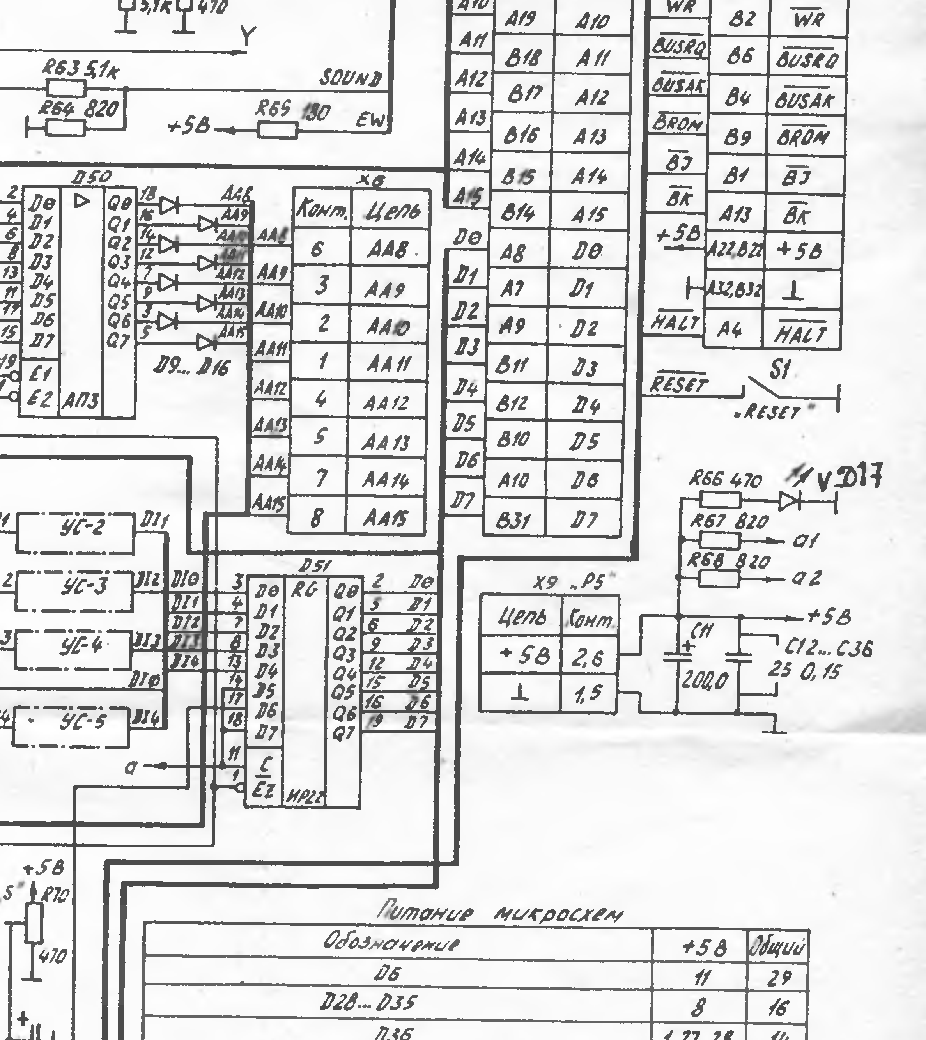
schematics/tiles/_right_connectors_bot.png
