anatoliegolovco/s4/schematics/tiles/_right_connectors_top.png

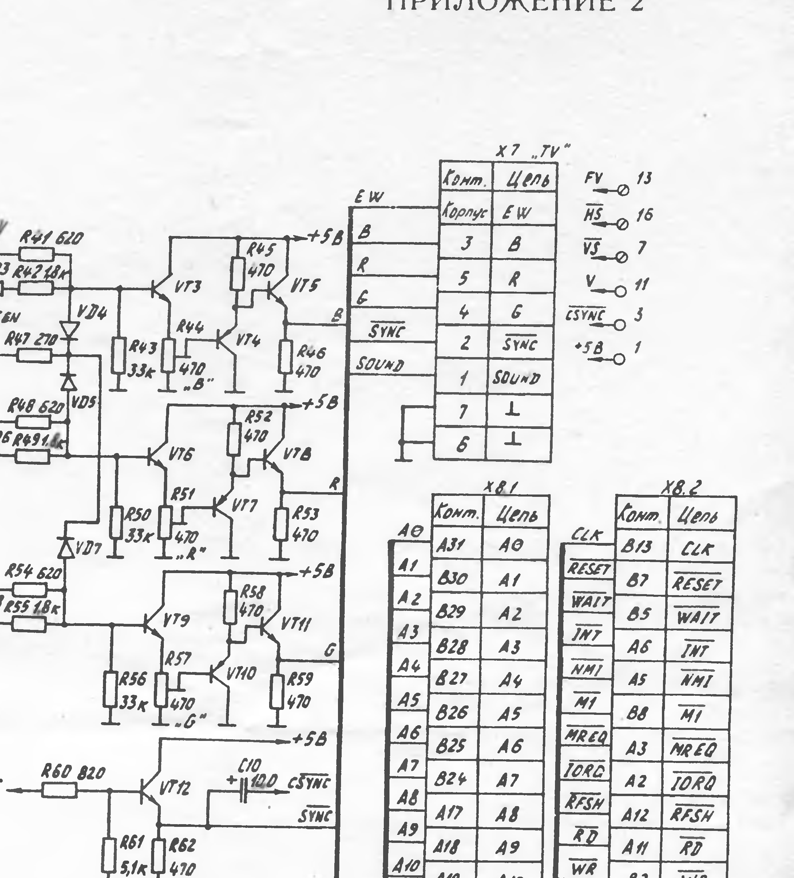
schematics/tiles/_right_connectors_top.png
