anatoliegolovco/s4/schematics/tiles/t_r1c1.png

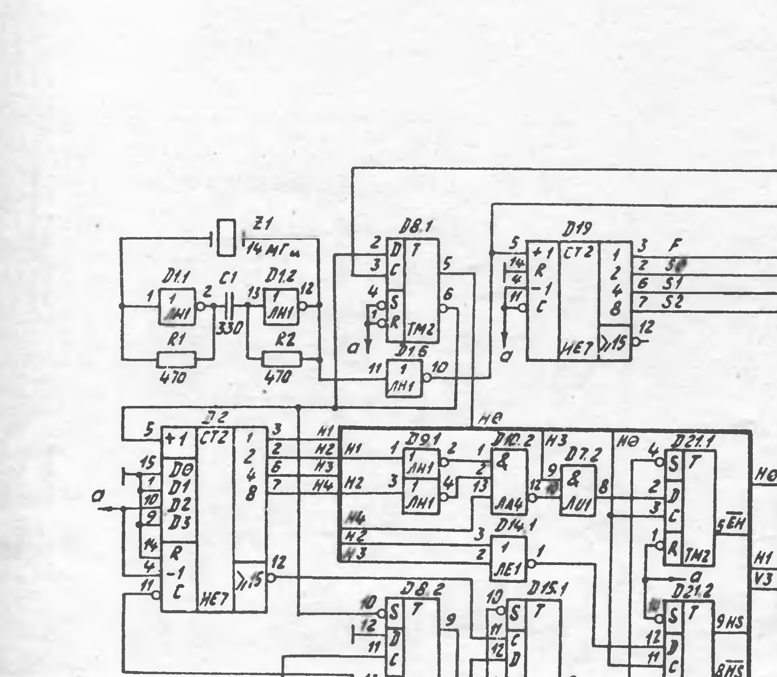
schematics/tiles/t_r1c1.png
