anatoliegolovco/s4/schematics/tiles/t_r1c2.png

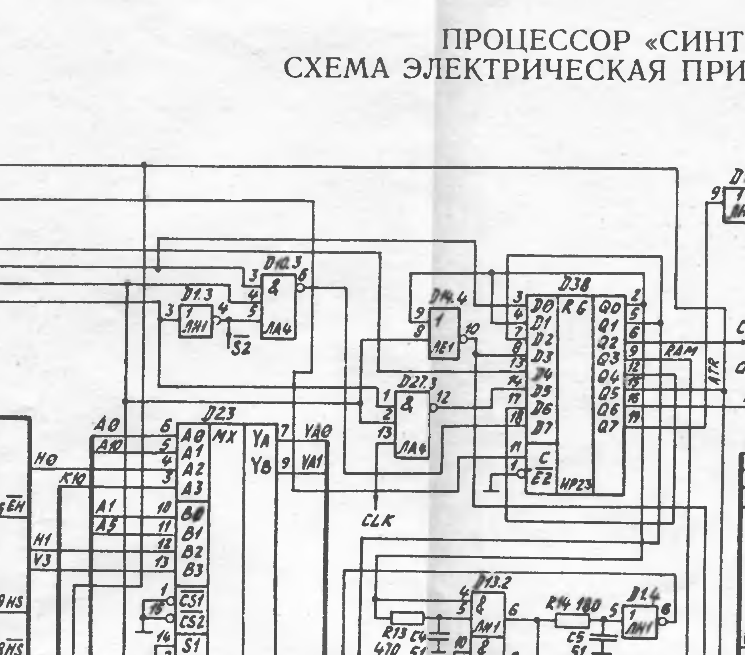
schematics/tiles/t_r1c2.png
