anatoliegolovco/s4/schematics/tiles/t_r1c3.png

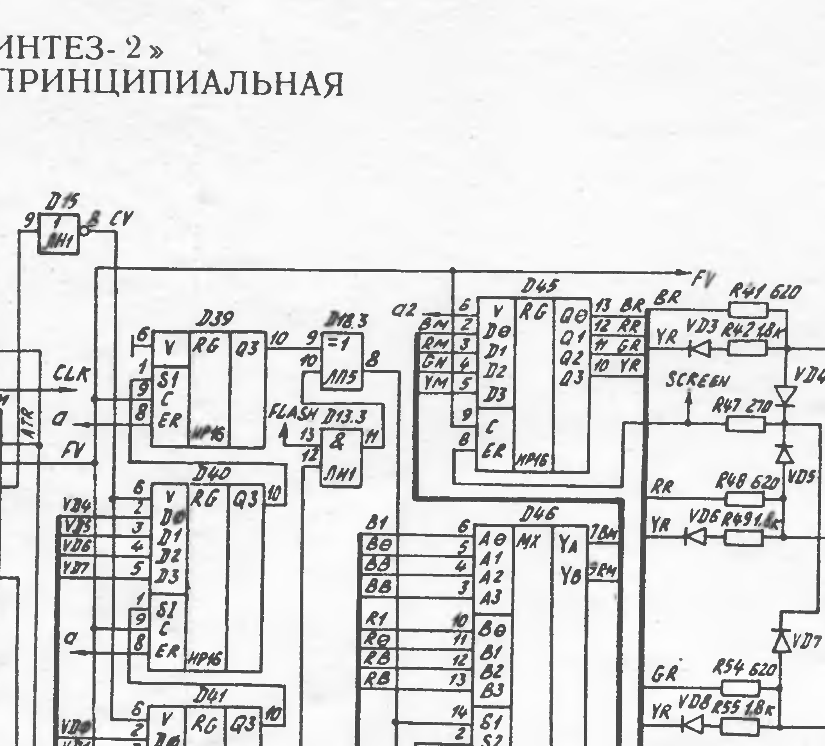
schematics/tiles/t_r1c3.png
