anatoliegolovco/s4/schematics/tiles/t_r1c4.png

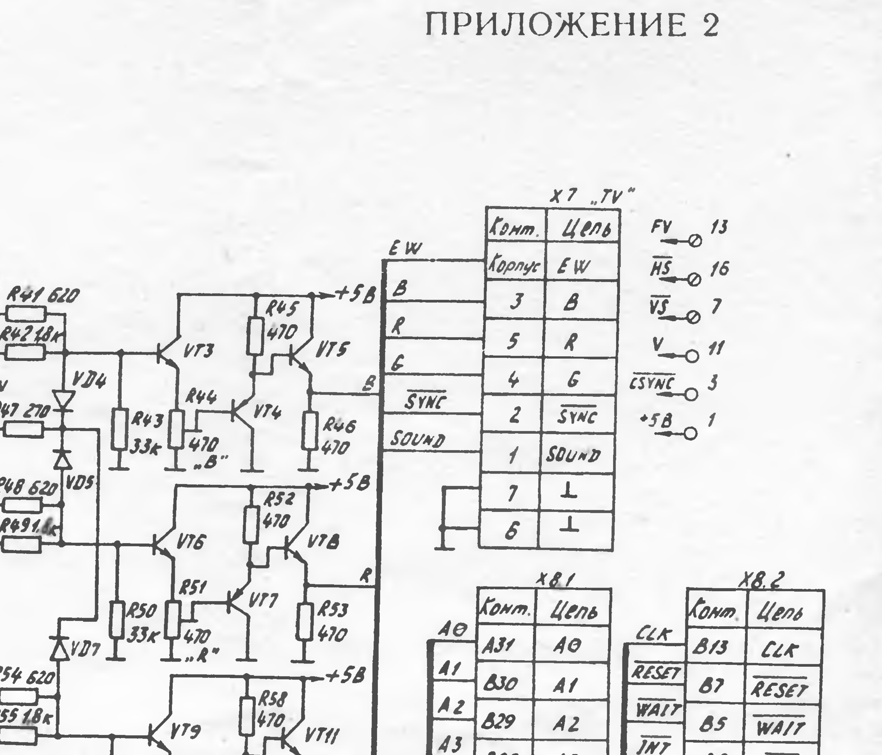
schematics/tiles/t_r1c4.png
