anatoliegolovco/s4/schematics/tiles/t_r2c1.png

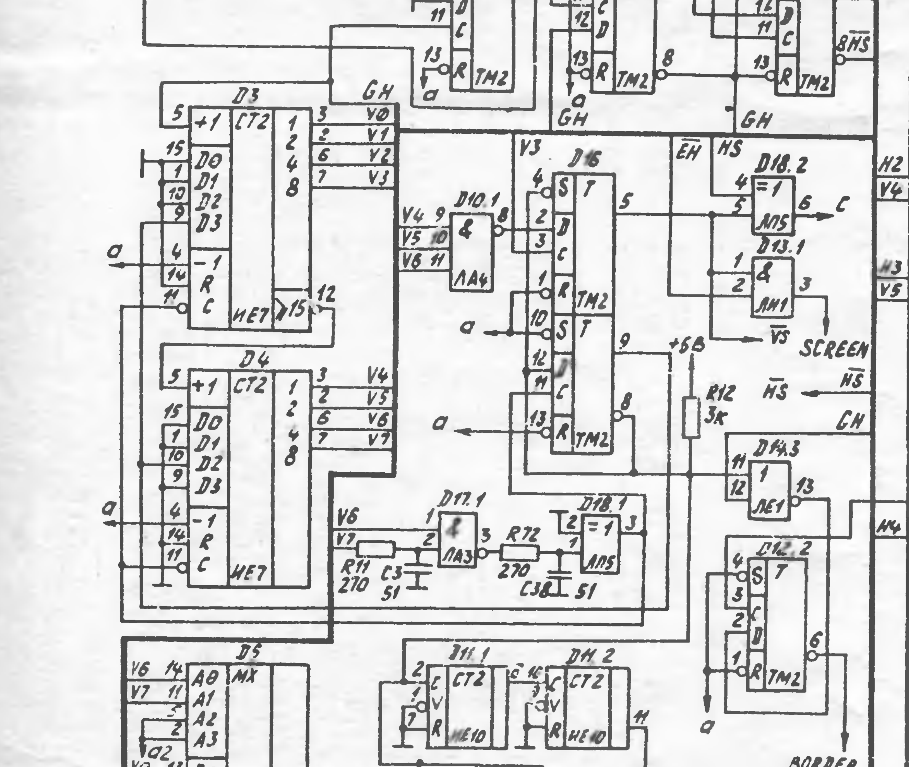
schematics/tiles/t_r2c1.png
