anatoliegolovco/s4/schematics/tiles/t_r2c2.png

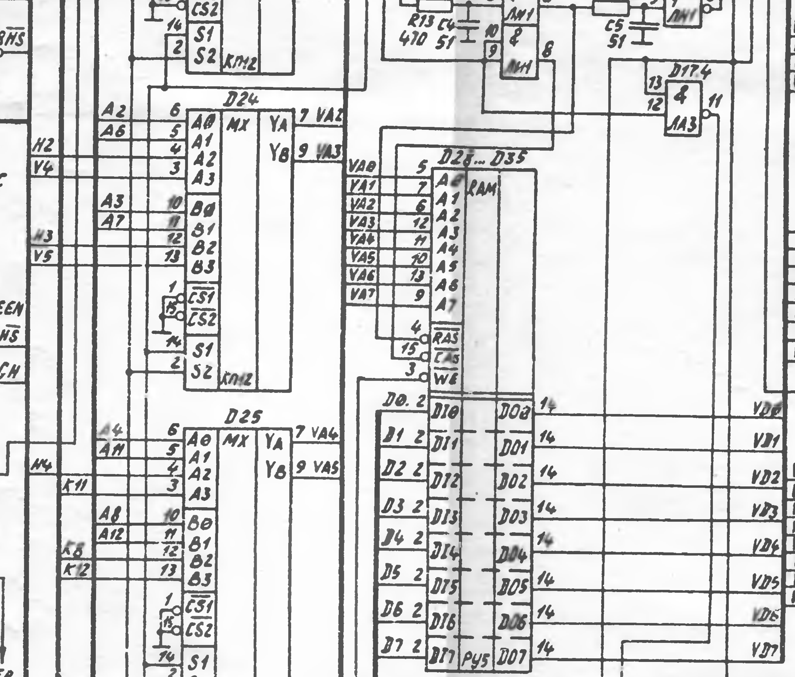
schematics/tiles/t_r2c2.png
