anatoliegolovco/s4/schematics/tiles/t_r2c4.png

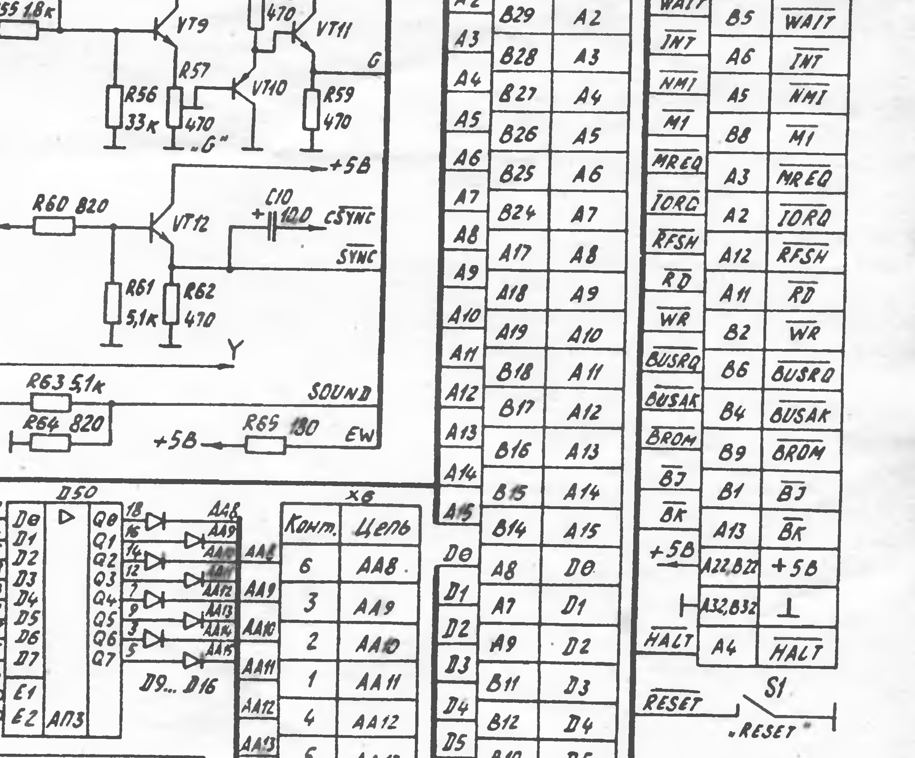
schematics/tiles/t_r2c4.png
