anatoliegolovco/s4/schematics/tiles/t_r3c2.png

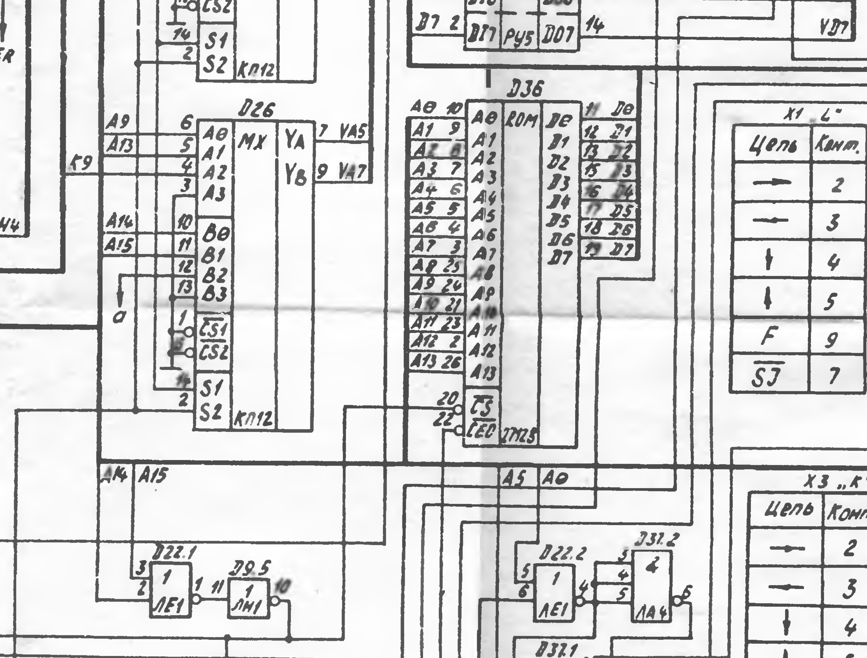
schematics/tiles/t_r3c2.png
