anatoliegolovco/s4/schematics/tiles/t_r3c3.png

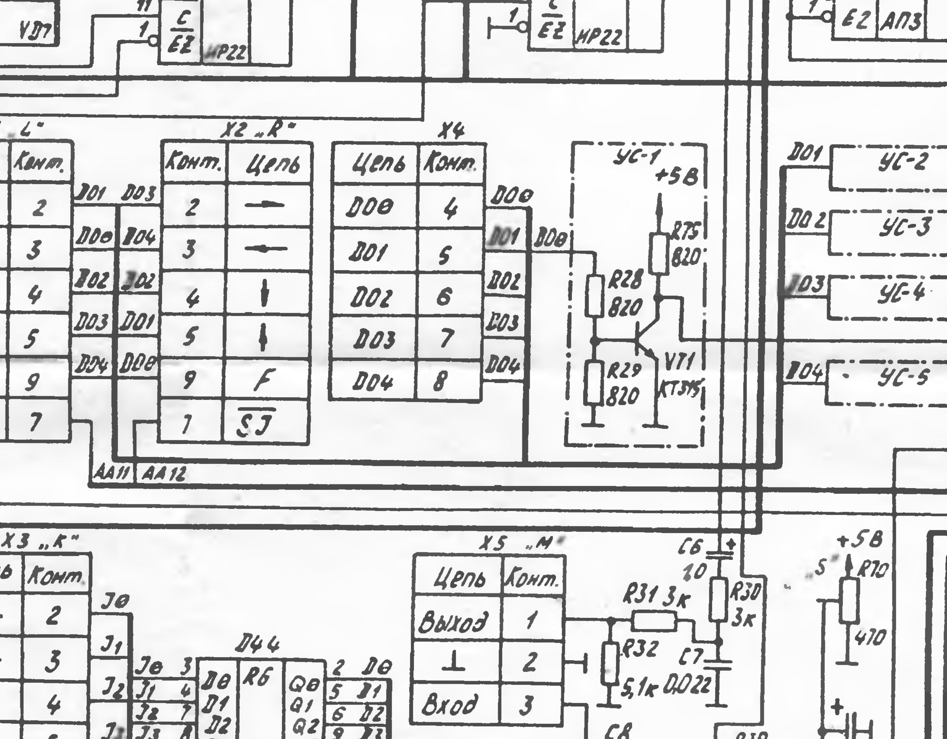
schematics/tiles/t_r3c3.png
