anatoliegolovco/s4/schematics/tiles/t_r3c4.png

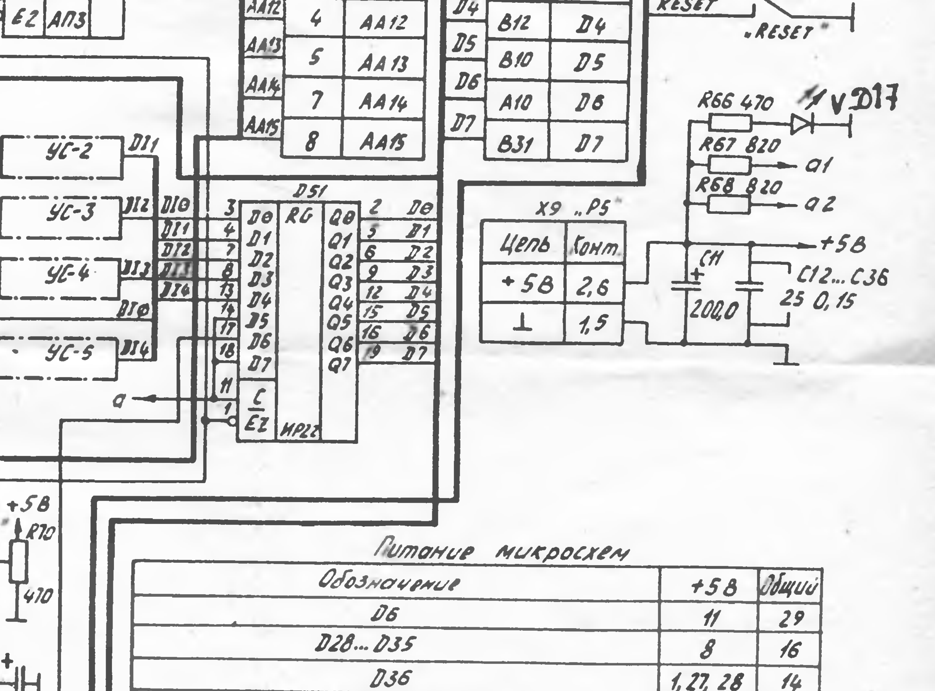
schematics/tiles/t_r3c4.png
