anatoliegolovco/s4/sim/monitor/boot-screen.png

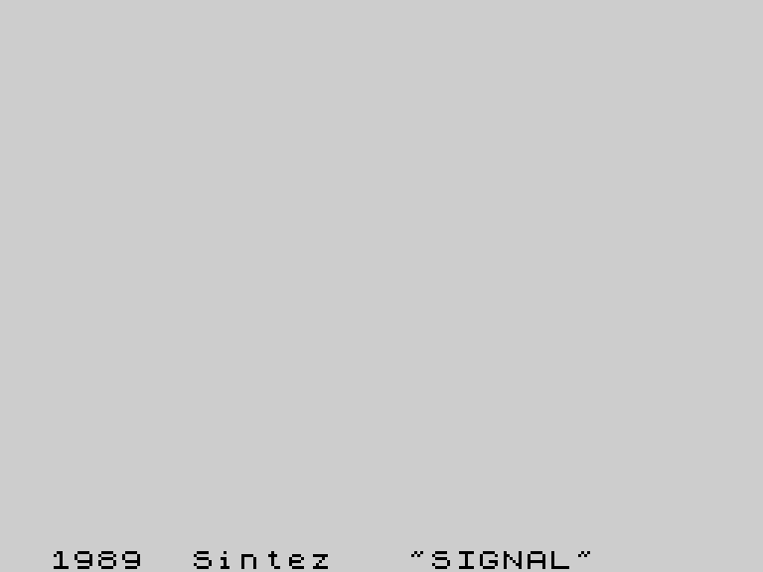
sim/monitor/boot-screen.png
