anatoliegolovco/s4/docs/ledger/sourcing/README.md

# Topic: sourcing

- **Created:** 2026-06-13
- **Status:** active

## Scope

Procurement of physical parts for the fabricated board: the Z80, Class-1 modern
logic, and analog/timing-sensitive parts; fabs reachable from Moldova.

## Questions

| Question file | Title | Status | Opened | Resolved |
| --- | --- | --- | --- | --- |
| [`z80-part-selection.md`](./z80-part-selection.md) | Which Z80 part for the physical build? | open | 2026-06-13 | — |
| [`datasheet-collection.md`](./datasheet-collection.md) | Where are the datasheets and key parameters? | resolved | 2026-06-13 | 2026-06-13 |
| [`reference-materials-intake.md`](./reference-materials-intake.md) | What primary-source materials do we have? | resolved | 2026-06-13 | 2026-06-13 |
