anatoliegolovco/s4/docs/ledger/project-setup/README.md

# Topic: project-setup

- **Created:** 2026-06-13
- **Status:** active

## Scope

Everything about standing up the repository: documentation structure, the
ledger, templates, conventions, and project tooling. Decisions here shape how
the rest of the project is recorded and built.

## Questions

| Question file | Title | Status | Opened | Resolved |
| --- | --- | --- | --- | --- |
| [`documentation-structure.md`](./documentation-structure.md) | How should docs and the discussion ledger be structured? | resolved | 2026-06-13 | 2026-06-13 |
