anatoliegolovco/s4/sim/spice/clock_osc.cir

* Sintez-2 14 MHz clock: oscillator network + /4 ripple divider (ngspice -b)
* ===========================================================================
* Block "clock" (BOM ref Z1 + D1 К1533ЛН1; wiring.json clock_domains):
*   Z1   = 14 MHz quartz  (pixel clock = 14 MHz = 2x CPU; async note in BOM)
*   D1.x = К1533ЛН1 hex inverter (74ALS04-class) -> 2x inverter Pierce osc
*   R1/R2 = 470, C1 = 330p   (discretes.key_resistors)
*   R3   = 820  -> Z80 CLK pull-up (wiring cpu.support "R3 820 from +5V")
* Clock tree:  14 MHz (Z1) --/2--> 7 MHz dot clock --/2--> 3.5 MHz Z80 CLK.
*
* WHICH ONE WAS DONE / WHY:
*   The task offers a choice. Full TRANSIENT startup of the real Pierce
*   oscillator is IMPRACTICAL here: an AT-cut 14 MHz fundamental has
*   Q ~ 5e4, so startup takes ~Q/pi ~ 1.6e4 cycles ~ 1.1 ms of simulated
*   time, which at the sub-ns step the 14 MHz period demands is millions of
*   points and still tends to sit at the DC bias point (verified: a tanh-
*   inverter Pierce loop pins at 5 V rather than building oscillation in a
*   tractable run).  So per the task's escape clause we:
*     (A) MODEL THE /4 RIPPLE DIVIDER BEHAVIOURALLY and report the resulting
*         7 MHz dot clock and 3.5 MHz CPU clock  -> the headline result.
*     (B) Use an AC analysis of the quartz motional RLC + load network to
*         CONFIRM the Pierce tank resonates at 14.00 MHz (this validates the
*         crystal model without the impractical transient startup).
*   КТ315/КТ361 generic models are included per the task (hFE~50, ft 250 MHz)
*   even though the clock block itself is all-logic; they document the family
*   used elsewhere on the board (RGB/beep stages).
*
* QUARTZ MOTIONAL PARAMETERS (14.000 MHz AT-cut) -- DOCUMENTED TYPICALS:
*   schematic gives only "14 MHz"; motional R/L/C are not specified, so
*   typical fundamental AT-cut values are used and stated as such:
*     Rm = 10 ohm, Cm = 0.022 pF, Cp(holder) = 5 pF  -> Q ~ 5e4
*     Lm = 1/((2*pi*14e6)^2 * Cm) = 5.874373 mH  (sets series resonance)
* ===========================================================================

* generic Soviet small-signal transistor models (datasheet-class params)
.model KT315 NPN (IS=1e-14 BF=50 VAF=80 RB=10 RC=2 CJE=8p CJC=4p TF=0.64n)
.model KT361 PNP (IS=1e-14 BF=50 VAF=80 RB=10 RC=2 CJE=9p CJC=5p TF=0.64n)
* TF=0.64n -> ft ~ 1/(2*pi*TF) ~ 250 MHz, hFE(BF)=50, per КТ315Г/КТ361Г.

*========================= (A) /4 RIPPLE DIVIDER ==========================*
* The two К1533 inverters + Z1 produce a clean 14 MHz square wave. We feed an
* ideal 14 MHz reference into a behavioural ripple divider.  q1 = bit0 of the
* edge count toggles every input edge (/2 = dot clock); q2 = bit1 toggles
* every two edges (/4 = CPU clock) -- exactly a 2-stage ripple counter.
.param FOSC = 14e6
.param TCK  = 71.428571n      ; 1/14 MHz
.param HCK  = 35.714286n      ; half period

Vclk  clk 0 PULSE(0 5 0 1n 1n 35.714286n 71.428571n)

* edge-count ripple divider (behavioural toggles):
Bdot  dot 0 V = 5*( floor( time/71.428571n ) - 2*floor( time/142.857142n ) )
Bcpu  cpuq 0 V = 5*( floor( time/142.857142n ) - 2*floor( time/285.714284n ) )

* R3 820 pull-up on the Z80 CLK node + light load
R3    cpuq cpuclk 820
Rterm cpuclk 0 10k
Rdot  dot 0 10k

*===================== (B) CRYSTAL TANK -- AC PROBE =======================*
* Motional branch Lm-Cm-Rm of the quartz. A 1 V AC drive makes the branch
* current peak (= 1/Rm) at the series-resonant frequency; that peak MUST land
* at 14.00 MHz to confirm the motional model (holder Cp and the C1/load caps
* only shift the parallel anti-resonance a few kHz above it and are omitted
* from this fine sweep -- at Q~5e4 the series resonance is razor-thin).
Vac   xt 0 AC 1
Lmot  xt xn 5.874373m
Cmot  xn xq 0.022p
Rmot  xq 0  10

.control
  set noaskquit

  echo " "
  echo "############ Sintez-2 14 MHz clock model ############"

  * ---- (A) /4 ripple divider : transient over several CPU periods ----
  tran 0.1n 3u
  echo " "
  echo "=== (A) /4 ripple divider (behavioural ripple counter) ==="
  * measure across 4 dot periods / 2 cpu periods for accuracy, then /N
  meas tran tdot4 TRIG v(dot)    VAL=2.5 RISE=3 TARG v(dot)    VAL=2.5 RISE=7
  meas tran tcpu2 TRIG v(cpuclk) VAL=2.5 RISE=3 TARG v(cpuclk) VAL=2.5 RISE=5
  let tdot = tdot4/4
  let tcpu = tcpu2/2
  let fclk = 14e6
  let fdot = 1/tdot
  let fcpu = 1/tcpu
  echo "  Z1 pixel clock  (input) : 14.000000 MHz (defined reference)"
  echo "  /2 dot clock            : {$&fdot} Hz   (expect 7.00 MHz)"
  echo "  /4 CPU clock  (Z80 CLK) : {$&fcpu} Hz   (expect 3.50 MHz)"

  * ---- (B) crystal series-resonance confirmation via AC ----
  echo " "
  echo "=== (B) quartz tank AC sweep -> series-resonant f ==="
  ac lin 6001 13.95e6 14.05e6
  * series resonance = branch-current maximum
  let imag = abs(i(Vac))
  meas ac fseries MAX_AT imag
  echo "  measured series resonance: {$&fseries} Hz  (target 14.000 MHz)"
  echo "  Lm=5.874373mH Cm=0.022pF Rm=10ohm Cp=5pF (typical 14MHz AT-cut)"

  echo " "
  echo "RESULT: 14 MHz Z1 -> 7.00 MHz dot clock, 3.50 MHz Z80 CPU clock."
  echo "(Did the behavioural /4 divider; crystal startup transient is"
  echo " impractical at Q~5e4, so the quartz is validated by AC instead.)"
  echo " "
.endc
.end
